LeweeLewee/Decca/mechanical/Drawings/Decca_IEC_C14_Mounting_Plate_Work_Handover.md

# Work Handover — Decca IEC C14 Mounting Plate

> **SUPERSEDED 2026-09-06.** The Rev A build described by the original handover was completed but **failed physical review** because its rectangular C14 opening did not properly enclose the actual inlet profile. Do not repeat or release Rev A.
>
> The active design is **Rev B**, controlled by `mechanical/Drawings/Decca_IEC_C14_Mounting_Plate_Spec_revB.md` and documented in `mechanical/Drawings/Decca_IEC_C14_Mounting_Plate_revB_Build_Report.md`.
>
> Rev B uses all four supplied profile measurements: 27.14 mm overall/long flat, 19.50 mm overall height, 16.00 mm opposite short flat and 14.00 mm straight side. These derive each angled side as 5.57 mm run × 5.50 mm rise = 44.638°. Nominal corners are R2.00 at the two long-flat corners and R0.40 at the other four. The production opening applies 0.25 mm normal clearance and is rotated 90° in the plate.
>
> Rev B CAD and exported STEP/STL pass 15/15 checks. Status remains **CAD PASS / physical prototype fit pending**.

The original Rev A handover has been intentionally replaced by this supersession notice so an automated worker cannot accidentally execute the rejected rectangular-opening design. Historical Rev A geometry, rationale and failure evidence remain in `Decca_IEC_C14_Mounting_Plate_Spec_revA.md` and `Decca_IEC_C14_Mounting_Plate_revA_Build_Report.md`.
