LeweeLewee/Decca/mechanical/Drawings/Decca_OLED_Display_Mount_Topology_revP.md

# Decca OLED Display Mount — Rev P Topology Review (pre-CAD gate)

Stage 1 deliverable required by `Decca_OLED_Display_Mount_CAD_Review_revO.md` §11.
No Fusion geometry may be generated until this section is clean.

> **Rev P.2 — CORRECTED 2026-08-29 after a physical retention failure.**
> The printed Rev P.1 carrier failed its retention test: the OLED falls forward
> through the loose carrier. The failure is **architectural, not a tolerance
> adjustment**. §0 records it; §1–§10 are the corrected topology and supersede
> the Rev P.1 text entirely.
>
> **Rev P.2 then PASSED physically** for OLED retention and Perspex tolerance.
> §1–§10 therefore describe validated hardware and are carried forward
> unchanged.
>
> **Rev P.3 — BOUNDED AMENDMENT 2026-08-29.** Two integration failures against
> the radio, neither touching the validated OLED architecture:
>
> - **§11** the continuous end rail and its cable-tie projection collide with
>   the retained original Decca lighting unit and are deleted;
> - **§12** the original front bolts have a non-standard thread, so the whole M2
>   heat-set-insert architecture is deleted and the original bolts and their
>   matching nuts are reused with a captive hex pocket.
>
> **Rev P.4 — BOUNDED CORRECTION 2026-08-29.** Two corrections to Rev P.3,
> again leaving the validated OLED architecture alone:
>
> - **§11.5** the synthetic lighting-unit keepout component is **deleted**. Its
>   boundary was asserted from the carrier's own pedestals, so it could never
>   have caught a real collision, and shipping it in the browser, the assembly
>   STEP and the manufacturing pack misrepresented the assembly. The physical
>   rail cut it was invented to justify is kept exactly as printed;
> - **§13** the open rear window is **closed** by an integral opaque rear light
>   shield, part of the carrier, with a single local four-pin/header opening.
>   §6 is amended accordingly: release was never rearward, and still is not.
>
> **Rev P.5 — MANDATORY AMENDMENT 2026-08-29.** Brief §5.3 and §8.4 together.
> These interact, so they are applied as one controlled update:
>
> - **§14** both plain locating posts are **deleted** and replaced by sprung
>   locating-and-retaining posts. Every one of the four PCB mounting holes now
>   holds a split sprung post. No plain-post parameter, body, branch, probe or
>   report entry survives;
> - **§15** the complete OLED reference is rotated **180° in plane**, so the
>   four-pin connector is at the **bottom**, and the visible active area is
>   dropped until its bottom edge meets the Perspex opening bottom edge. The
>   panel-fixed holes do **not** move;
> - **§16** the carrier drops to **6.00 mm** deep, the finished rear opening
>   grows 25% to **14.00 × 4.19 mm**, and two integral **light-block** baffles
>   are added beside it.
>
> **Nothing numeric is inherited.** The 2.00 mm depth reduction shortens every
> sprung cantilever, so both pairs are re-solved from the finished solid.
> §1–§10 remain the architecture; their *numbers* are superseded by §14–§16.

> **Rev P.5 MOUNTING-POINT CORRECTION, 2026-08-29.** Both carrier fixing
> centres move **7.00 mm toward the connector/open bottom** relative to the
> OLED-dependent group (`carrier_fix_y_from_previous = -7.00 mm`). The original
> Perspex holes do not move, so in the assembled frame the equivalent — and the
> only implementation that lands the carrier holes *on* the Perspex holes — is
> to raise the OLED bay and everything that depends on it by **+7.00 mm**.
>
> **This supersedes §15's active-area-bottom-to-opening-bottom rule**, and
> every PASS that depended on it. §17 records the correction and, plainly, what
> it does to the visible screen.

Baseline: `main` @ `d7ac584`, whose §5.3, §8.1, §8.2, §8.3, §8.4, §9, §10 and
§12 are authoritative over anything written on this branch before them.

---

## 0. The Rev P.1 retention failure — what actually went wrong

Rev P.1 inserted the OLED **from the rear**, moving forwards towards the
Perspex. Its four snap-finger shoulders sat at the **PCB rear plane** (z = −2.70)
and stopped motion in the **opposite** direction — rearward, back out of the
pocket. Once the board passed those shoulders there was **no positive feature of
any kind** preventing further forward travel.

The only thing holding the module in a loose carrier was four 0.10 mm edge-grip
tongues pressing on the PCB **edge**, relying on an assumed PETG friction
coefficient. The Rev P.1 gate checked:

- that the rear shoulders exist — **they do, and they restrain the wrong way**;
- that the tongues stop behind the PCB front plane — **they do, which is exactly
  why they cannot stop forward travel**;
- that computed friction (0.55 N) exceeds module weight (0.039 N) — **a
  calculation, not a geometric stop**.

Nowhere did it demonstrate a positive geometric stop against forward movement,
because there was not one to demonstrate. The physical print settled it: the
screen falls out forwards.

**Conclusion.** Friction between a printed tongue and a PCB edge is not
retention. The gate must require *geometry that physically blocks the motion*,
and the module must be inserted from the side it is restrained on.

The following are **not** acceptable fixes and are not attempted: increasing
`finger_grip`, revising the assumed friction coefficient, increasing spring
force, or adding another rear-loaded edge finger. All four leave the
architectural defect in place.

### What survives from Rev P.1

The structural half of Rev P.1 was sound and is retained unchanged: the M2 load
path in parallel with the module, the direct carrier-to-Perspex hard stop, the
0.30 mm optical chain, the ≤ 1.00 mm front-side protrusion budget, the open
rear, active-area centring, the single printed carrier plus the Rev N bezel, and
the invariant-based way of proving that nothing structural sits in front of the
PCB.

### What is deleted

The four PCB-edge friction fingers, their shoulders, their 0.10 mm tongues,
their four Ø2.20 mm radial prise holes, and the friction-versus-weight
acceptance gate. None of them appears anywhere in Rev P.2.

---

## 1. Side section — insertion direction, both axial stops, the load path

Section on the plane x = +15.00 (through a sprung locating post), looking
along −X. `+Z` is forward, out of the fascia. `z = 0` is the rear face of the
Perspex. **The module is inserted from the FRONT, moving rearward (−Z).**

```text
                        FRONT (viewer)  —  INSERTION SIDE
   ═══════════════════════════════════════════════════════════   z = +3.00
     ORIGINAL bolt head bears here          ORIGINAL PERSPEX 3.00 mm
   ═════════════╤═══════════════════════════════════════╤═════   z =  0.00  <- DATUM A
                |                                       |           carrier hard stop
                |         v  v  v  MODULE INSERTED      |           (seating plane)
                |         v  v  v  FROM THIS SIDE       |
                |                                       |
                |        <- optical gap 0.30 mm ->      |       z = −0.30  glass front
                |   ┌────────────────────────┐    /^\   |       z = −0.40  nose tip
   ┌────────────┤   |       OLED GLASS       |   /   \  |       (Ø2.60, 0.40 clear
   |            |   |   (0.80 proud of PCB)  |  | Ø3.2| |        of the Perspex)
   |  CARRIER   |   |                        |  ├─────┤ |       z = −0.75  land
   |    RIM     |   ├────────────────────────┤  ├█████┤ |       z = −1.00  <- SNAP HOOK
   |  (3.00)    |   |        OLED PCB        |  |     | |        retaining face, square,
   |            |   |        1.60 mm         |  |     | |        0.10 mm axial clearance
   |            |█  |                        |  |Ø2.80| |       z = −1.10  PCB front face
   |            |█  |                        |  |shaft| |       z = −1.20  fwd material
   |            |█  └────────────────────────┘  |     | |                  limit (rim)
   |            |█══════════════╤═══════════════╪═════╪═|       z = −2.70  <- DATUM B
   |            |█  ███████████ | FIXED DATUM   |     | |        PCB REAR FACE seats on
   |            |█  ██pedestal█ | PAD Ø6.0/Ø4.8 |     | |        FIXED, RIGID pads
   |            |█  ███████████ └───────────────┤     | |       z = −3.00  pedestal top
   |            |█  ██████████  Ø4.80 root  ████|     | |
   |            |█  ██████████     relief   ████|     | |        (the relief is now
   |  M2 boss   |█  ██████████  (3.20 deep) ████|  \_/| |         BEHIND the PCB — the
   |  + insert  |█  ████████████████████████████ \___/  |         glass cannot constrain
   |            |█  ██████████████ R0.80 fillet ────────┘         its depth any more)
   |            |█  ████████████████████████████████████  z = −5.90  post root
   |            |█  ████████████████████████████████████
   └────────────┴──█████████████████████████████████████         z = −8.00  carrier rear
                        REAR (cabinet)  —  OPEN                  z = −10.80 header extent

   █ = rigid carrier body (pocket wall / pedestal).
   The ONLY sprung element anywhere in the carrier is the split post nose.
```

### The two positive axial stops

| Direction | Stopped by | Nature |
|---|---|---|
| **Rearward** (−Z, the insertion direction) | four **fixed datum pads** at z = −2.70, rigid parts of the carrier body, concentric with the four PCB mounting holes | rigid solid-to-solid seat, no spring anywhere in the path |
| **Forward** (+Z, the direction Rev P.1 failed in) | two **sprung post hooks**, Ø3.20 barb over a Ø3.00 hole = **0.10 mm radial geometric overlap**, square retaining face at z = −1.00 | positive geometric interference — the retaining face is square and cannot cam, so an axial pull cannot release it |

Neither stop touches the glass:

- the rearward stop acts on the PCB **rear** face, 1.60 mm behind the glass;
- the forward stop acts on the PCB **front** face **inside the Ø3.00 mounting
  hole**, which is a keep-out on both faces of the board by definition;
- the glass front face is at z = −0.30 and nothing but air is in front of it.

**Neither stop is friction.** Friction plays no part in Rev P.2 retention and no
friction calculation appears in the acceptance gate.

### M2 load path — unchanged from Rev P.1

```text
ORIGINAL bolt head -> Perspex front face -> Perspex (3.00) -> Perspex rear
                   -> carrier seating rim + boss pad  (z = 0, DATUM A)
                   -> captive ORIGINAL nut -> original bolt thread

(Rev P.3: the M2 heat-set insert this line used to name is deleted - see 12)
```

The forward-most carrier material anywhere is z = 0. The forward-most module
material is the glass front face at z = −0.30. The carrier bottoms out on the
Perspex 0.30 mm before anything can reach the glass and 1.10 mm before anything
can reach the PCB. Carrier and module are in **parallel**, never in series, so
**M2 torque cannot reach the module** — it cannot alter OLED depth, preload the
glass or preload the PCB.

The snap hooks are not in the load path either: their tips stop at z = −0.40,
0.40 mm short of the Perspex, so tightening the screws never touches them.

---

## 2. Plan view — locating posts, datum pads, rear access

Rear view (looking forward, −Z). Dimensions in the aperture-centre frame.

```text
                    y = +30.60  ┌───────────────────────────────┐
                                |   cable-tie flange   ▭    ▭   |  tie slots x ±10.50
                    y = +24.60  ├───────┬───────────────┬───────┤
                                |       | wire notch    |       |  13.0 x 1.5 rear-open
                    y = +21.60  |   ┌───┴───────────────┴───┐   |  <- aperture edge
                    y = +21.00  |   |                       |   |  <- pocket wall
                    y = +20.75  |   ├───────────────────────┤   |  <- PCB top edge
                                |   |  ╭─╮   ┌───────┐  ╭─╮ |   |
                    y = +18.25  |   |  |S|   | header|  |S| |   |  <- SPRUNG POSTS
                                |   |  ╰─╯   └───────┘  ╰─╯ |   |     x ±15.00
                                |   |   ^ Ø8.6 pedestal ^   |   |
                                |   |                       |   |
   ●  M2 x = −24.50             |   |      OLED  PCB        |   |         M2 x = +24.50 ●
   y = 0 ──────────────────────-|   |     35.40 x 33.50     |   |-────────────────── y = 0
                                |   |   centre y = +4.00    |   |
                                |   |  ┌─────────────────┐  |   |
                                |   |  |  ACTIVE  AREA   |  |   |  29.42 x 14.70
                                |   |  |  centred (0,0)  |  |   |  <- OPTICAL DATUM
                                |   |  └─────────────────┘  |   |
                                |   |  ╭─╮           ╭─╮    |   |
                    y = −10.25  |   |  |P|           |P|    |   |  <- PLAIN POSTS
                                |   |  ╰─╯           ╰─╯    |   |     x ±15.00
                    y = −12.75  |   ├───────────────────────┤   |  <- PCB bottom edge
                    y = −13.00  |   |                       |   |
                    y = −13.60  |   └───────────────────────┘   |
                    y = −16.60  └───────────────────────────────┘
                                x = −21.55                x = +21.55
                                    (carrier rim, ±28.30 over the M2 ears)

   S = split SPRUNG locating post, Ø2.80 shaft / 0.70 slot / Ø3.20 barb
   P = PLAIN locating post, Ø2.70, top at z = −1.20 — never crosses the PCB
       front plane, so it is unconditionally clear of the glass
   Each post stands in a Ø4.80 root relief, on a Ø8.00 pedestal, ringed by a
   Ø6.00/Ø4.80 fixed datum pad at z = −2.70.
   Rev P.4: the rear of the bay is CLOSED by the 1.20 mm integral light shield
   (§13), with one local four-pin/header slot, x −5.60 … +5.60, y +17.15 upward.
   Header and cable exit through that slot; removal is forward, not rearward.
```

### Why the sprung pair is on the header side and the plain pair is not

The brief's default arrangement, and the reason for it, is this design's single
remaining risk:

| Hole pair | y | Modelled glass edge | Margin to a Ø3.20 nose | Post type |
|---|---:|---:|---:|---|
| Header side ("wide") | +18.25 | +13.95 | **+2.70 mm** | **sprung** |
| Display side ("narrow") | −10.25 | −9.05 | **−0.40 mm (fouls)** | **plain** |

On the modelled envelope the glass **overhangs the display-side mounting holes**.
That pair therefore gets **plain posts that stop at z = −1.20**, 0.10 mm behind
the PCB front plane. Nothing there ever crosses into glass territory, whatever
the real envelope turns out to be — the risk is removed by geometry, not by a
number.

Rev K put sprung pegs in the narrow pair on **0.20 mm of assumed glass
clearance** and called it validated. That unmeasured dependency is **not**
recreated here.

---

## 3. Locating and retaining posts — geometry and the Rev D/K inheritance

Starting values taken from the printed Rev D / Rev K post development, then
**recalculated from the finished Rev P.2 geometry** as the brief requires.

### 3.1 Sprung locating posts — x = ±15.00, y = +18.25

| z range | feature | Ø | note |
|---|---|---:|---|
| −5.90 … −5.10 | R0.80 root fillet | 2.80 → 4.40 | inside the Ø4.80 relief, top 2.40 mm behind DATUM B |
| −5.90 … −1.00 | split shaft | **2.80** | 0.10 mm radial clearance in the Ø3.00 hole |
| −1.10 … −1.00 | axial clearance zone | 2.80 | **0.10 mm** — the hook does not clamp the PCB |
| **z = −1.00** | **retaining face — square, rearward-facing** | 2.80 → **3.20** | **0.10 mm radial overlap = the forward stop** |
| −1.00 … −0.75 | full-diameter land | 3.20 | 0.25 mm, thicker than a print layer |
| −0.75 … −0.40 | insertion lead-in cone | 3.20 → 2.60 | 40.6° from the axis |
| slot | full height, 0.70 mm wide, normal to Y | | halves deflect **inward**, never outward |

### 3.2 Plain locating posts — x = ±15.00, y = −10.25

| z range | feature | Ø |
|---|---|---:|
| −3.70 … −2.90 | R0.80 root fillet | 2.70 → 4.30 |
| −3.70 … −1.65 | shaft | **2.70** (0.15 mm radial clearance) |
| −1.65 … −1.35 | entry chamfer | 2.70 → 2.10 |

Top face at z = −1.35 — **0.25 mm behind the PCB front plane**, so the plain
posts satisfy the original prohibition without needing the controlled exception
at all. 0.10 mm (the generic `forward_setback`) is too thin to trust on an FDM
post top when the modelled glass overhangs these holes; 0.25 mm costs nothing
and still engages 1.35 mm of the 1.60 mm board.

### 3.3 Reused, changed, and why

| Rev D / Rev K value | Rev P.2 | Change and reason |
|---|---|---|
| sprung shaft Ø2.80 | **Ø2.80** | reused unchanged — printed and fit-tested at Rev D |
| split slot 0.70 | **0.70** | reused unchanged |
| barb Ø3.20, 0.10 mm radial hook | **Ø3.20, 0.10 mm** | reused unchanged — the brief's starting value |
| R0.80 root fillet | **R0.80** | reused unchanged |
| plain post Ø2.70 | **Ø2.70** | reused unchanged |
| root relief ≈ 1.00 mm | **3.20 mm (sprung) / 1.00 mm (plain)** | **changed.** In Rev D/K the relief sat *in front of* the PCB, so its depth was capped by the glass — that is exactly what forced Rev K's narrow pair down to a 0.40 mm relief on 0.20 mm of assumed clearance. In Rev P.2 the relief is **behind** the PCB, where the glass cannot constrain it at all, so its depth is set by strain instead. |
| hook land (Rev D: under one print layer) | **0.25 mm** | **changed.** A retaining face thinner than a layer is not a retaining face. |
| Rev D peak strain 1.64 % (a = 3.10) | **0.83 %** (a = 4.35) | consequence of the deeper relief |
| Rev K narrow pair on 0.20 mm assumed glass clearance | **deleted** | replaced by plain posts — the dependency is removed, not re-estimated |

### 3.4 Recalculated mechanics

Cantilever half-post, fixed at the top of the root fillet (z = −5.10), loaded at
the full-diameter land (z = −0.75): free length **a = 4.35 mm**, half-section
thickness t = (2.80 − 0.70)/2 = **1.05 mm**, PETG E = 2000 MPa.

| Quantity | Value |
|---|---:|
| Deflection to pass the barb, per half | 0.10 mm |
| **Peak strain, hole centred** | **0.83 %** |
| Deflection worst case, board hard to one side | 0.20 mm on one half |
| **Peak strain, worst case** | **1.66 %** |
| Strain limit | 3.00 % |
| Radial spring force per post at 0.10 mm | ≈ 3.9 N |
| Insertion force (40.6° cam, µ 0.30) | ≈ 6.1 N per post → **≈ 12.3 N total** |
| Seated deflection | **0.00 mm — the barb clears the PCB entirely** |
| Seated radial preload on the PCB | **zero** (0.10 mm shaft clearance in the hole) |
| Seated axial preload on the PCB | **zero** (0.10 mm clearance under the hook) |
| PCB bending from retention | **none** |
| Forward retention mechanism | **positive geometric overlap**, square face, cannot cam |
| Bearing area of the two hooks | ≈ 3 mm² → far beyond a 0.039 N module |

The seated state is the important line. Once the board is home, **every spring
in the carrier is fully relaxed**. The hooks stand clear of the PCB by 0.10 mm
and the shafts clear the holes by 0.10 mm radially, so the module is held by
four rigid pads at its rear and blocked by two relaxed hooks at its front, with
nothing squeezing, bending or preloading it.

---

## 4. Fixed rear datum pads

Four annular pads, **rigid parts of the carrier body**, top face at z = −2.70:

| | |
|---|---:|
| Position | concentric with the four Ø3.00 PCB mounting holes, x ±15.00, y +18.25 / −10.25 |
| Outer Ø / inner Ø | 6.00 / 4.80 |
| Nominal annulus area | 10.18 mm² each |
| Area actually on the PCB (clipped by the 35.40 x 33.50 outline) | ≈ 8.6 mm² each, **≈ 34 mm² total** |
| Supported by | Ø8.00 pedestals, z −8.00 … −3.00, merged into the pocket walls |
| Spring content | **none** — solid carrier body throughout |

Why these four locations and no others: they sit **inside the PCB's own
mounting-hole keep-outs**, which are component-free on both faces by
construction. Every earlier revision took its PCB datum from the board edge
band, which is an assumption about where components are not. This one is not an
assumption.

They span a 30.00 x 28.50 rectangle — the widest stable four-point pattern the
board offers — so the seated board cannot rock. Loading is the ≈ 12 N insertion
push only; nothing pushes the module rearward in service. 34 mm² at 12 N is
0.35 MPa.

---

## 5. Invariant P1′ — the controlled exception, stated as geometry

Rev P.1's invariant P1 said the aperture prism is empty forward of the PCB face.
Rev P.2 needs positive forward retention, so the invariant is **tightened to name
its own exception** rather than relaxed:

> **Invariant P1′.** Let `A` be the module-aperture prism
> `{ |x| ≤ 18.55, −13.60 ≤ y ≤ +21.60 }` and let `N` be the two nose envelopes
> `{ (x ∓ 15.00)² + (y − 18.25)² ≤ 1.60², −1.20 < z ≤ −0.40 }`. Then
>
> `Carrier ∩ A ∩ { z > −1.20 }  ⊆  N`
>
> and `N` lies strictly inside the two Ø3.00 PCB mounting-hole corridors.

Everything else satisfies the original prohibition unchanged:

| Carrier feature | z extent | satisfies P1′ because |
|---|---|---|
| Seating rim / frame | 0 … −8.00 | outside `A` |
| M2 bosses + ears | 0 … −8.00 | \|x\| ≥ 20.50, outside `A` |
| Cable-tie flange | 0 … −8.00 | y ≥ +24.60, outside `A` |
| PCB pocket walls | −1.20 … −8.00 | z ≤ −1.20 |
| Post pedestals, datum pads, root reliefs | −2.70 … −8.00 | z ≤ −1.20 |
| Plain post shafts and chamfers | −1.20 … −3.70 | z ≤ −1.20 |
| Sprung post shafts | −1.00 … −5.70 | cross z = −1.20 only inside `N` |
| **Sprung post noses** | **−1.20 … −0.40** | **the declared exception `N`** |

There is still **no carrier plate, seating land, structural shoulder or other
load-bearing feature** between the PCB front face and the Perspex. `N` carries no
load, sets no datum, and touches the PCB only when the module is being pulled
forwards out of the carrier.

### What `N` must be proven clear of

| `N` vs | Result | Basis |
|---|---|---|
| the Perspex | **0.40 mm clear** — nose tip z = −0.40, Perspex z ≥ 0 | modelled from the measured 3.00 mm panel |
| the Rev N bezel | **clear** — the bezel lip lies inside \|x\| ≤ 17.45, \|y\| ≤ 7.50; `N` is at y ≈ +18.25 | Rev N geometry, unchanged |
| the active display area | **9.30 mm clear** in Y | active area 29.42 x 14.70 on (0,0) |
| solder joints / tips | **8.49 mm clear** in X | tips at x −3.91 … +4.91 |
| the insertion and removal corridor | **clear** — the corridor is a pure ±Z translation and `N` sits inside the hole corridor it is meant to occupy | §6 |
| **the OLED glass** | **NOT DEMONSTRATED — see §7** | the glass X/Y envelope has never been measured |

---

## 6. Insertion and removal

Pure ±Z translation. No tilt, no rotation, no lateral shift — the only motion
whose swept envelope is exactly the module cross-section extruded along Z.

**Insertion** (carrier off the panel, **seating face towards you**):

1. Offer the module to the **front** of the carrier, glass towards the carrier,
   header at the top. The glass enters the open module aperture, which is
   0.85 mm larger than the PCB all round.
2. The two sprung barb tips (Ø2.60 at z = −0.40) enter the two header-side
   mounting holes first and align the board.
3. The PCB rear face enters the pocket at z = −1.20 (0.25 mm clearance).
4. The barbs cam inward 0.10 mm per half against the hole walls; the plain posts
   enter the display-side holes.
5. The PCB rear face lands on the **four fixed datum pads at z = −2.70**. Motion
   stops there — on rigid carrier body, not on a spring.
6. As the PCB front face passes z = −1.00 the two barbs snap fully clear and
   relax to zero deflection, standing 0.10 mm ahead of the PCB front face.
   Their tips reach z = −0.40, so 0.70 mm of nose stands proud of the board.

Only the two intended sprung noses deflect at any point in that sequence.
Everything else the module touches is rigid.

**Removal** (identified tool path):

1. Remove the two original bolts and lift the carrier off the Perspex.
2. From the front, squeeze each barb inward with fine-nose tweezers or snipe
   pliers — 0.10 mm per half. The barbs stand 0.70 mm proud of the PCB front
   face and are completely exposed, because nothing at all sits in front of the
   PCB.
3. With a barb pinched, lift that corner clear. The module aperture is 0.85 mm
   larger than the PCB on every side, so a spudger reaches the board edge at
   z = −1.20 all round and levers it forward.
4. If more purchase is wanted, the board's top edge (y = +20.75) overhangs the
   carrier's own termination (y = +20.50) by 0.25 mm and is reachable from the
   **open lighting-unit side**, which §11 deletes the rail from and §13 does not
   close. Push forward there.
5. The plain posts then slide straight out.

No prise holes, no special tool, and no rigid feature anywhere in the corridor.

**Rev P.4: the rear wall does not trap the module.** §13 closes the rear of the
bay, so the Rev P.3 rear push-out is gone. Nothing else changes, because the
release was never rearward:

| Requirement | How it is met with the rear wall present |
|---|---|
| the sprung posts are deliberately released | pinch both barbs 0.12 mm per half with fine-nose tweezers; 0.70 mm of each nose stands proud of the PCB front face |
| release is performed from the front or accessible sides | from the front through the module aperture, assisted if wanted from the open lighting-unit side |
| the OLED withdraws through the front/Perspex side | removal travel is **+Z**, the same straight line as insertion, reversed |
| neither PCB nor bonded glass contacts the rear wall | the wall's front face is at z = −6.80 and the PCB rear face never leaves z ≥ −2.70: **4.10 mm** of clearance, at every point of the sweep |

**Swept corridor expectations** (verified numerically in Stage 2):

| Swept body, ±Z | vs carrier | why |
|---|---|---|
| OLED glass | must be **CLEAR** | the aperture is empty forward of z = −1.20 except `N`; `N` is at y +18.25 |
| Solder tips @ 1.00 mm | must be **CLEAR** | tips at x −3.91 … +4.91, `N` at x ±13.40 … ±16.60 |
| Header body | must be **CLEAR** | pedestals at \|x\| 11.00 … 19.00; header at x ±5.00 |
| OLED PCB | **HIT expected**, at the two barbs only | the designed 0.10 mm snap deflection and nothing else |
| Four mounting-hole corridors | **HIT expected**, posts only | the posts are meant to be there |

---

## 7. The one blocking measurement — reported, not assumed

The brief is explicit: *if the real glass envelope cannot be demonstrated clear,
stop and report the missing measurement rather than assuming it.*

**It cannot be demonstrated. It is reported here, and it is not assumed away.**

| | |
|---|---|
| Missing dimension | the OLED glass X/Y envelope relative to the two **header-side** Ø3.00 mounting holes at (±15.00, +18.25) |
| Status in this repository | **never measured.** `oled_glass_w`, `oled_glass_h` and `oled_glass_off_y` are flagged NOT MEASURED in every revision since Rev B. The only measured glass dimension is `oled_glass_proud` = 0.80 mm. |
| Modelled value | glass top edge at y = +13.95 → **2.70 mm clear** of a Ø3.20 nose |
| Acceptance criterion | **the glass must not extend above y = +16.15** — it must stay clear of Ø4.20 circles centred on the two header-side mounting holes (nose Ø3.20 + 0.50 mm margin all round) |
| How to measure | with the module in hand, digital calipers: distance from each header-side mounting-hole centre to the nearest bonded-glass edge. One number, both ends. It must be **≥ 2.10 mm**. |
| Consequence if it fails | the sprung noses foul the glass. The design does **not** proceed to a print on an assumption. |

Evidence that is *suggestive* but is deliberately **not** treated as proof: the
front-face solder pads sit at y ≈ +17.95 … +19.15, and bonded glass cannot cover
solder pads, which bounds a rectangular glass panel below y ≈ +17.95. That bound
is 1.80 mm short of what the nose needs, and it rests on the pad position rather
than on the glass itself. It is not sufficient.

Note also what the modelled envelope implies: it puts the glass **0.40 mm over
the display-side mounting holes**, which would make the module unmountable with
any screw. The modelled numbers are therefore known to be untrustworthy in
exactly this region — a further reason not to lean on them.

**Gate: no corrected Rev P print until this single number is taken.** Everything
else in Rev P.2 is complete and validated; this is the one item standing between
the CAD and the printer.

Contingency if the measurement fails: move the sprung pair outboard along X
within the keep-out, or fall back to a non-hole forward stop bearing on the PCB
**corners** outside the glass footprint. Both are small changes to the generator;
neither is designed until the number exists.

### The other unmeasured inputs, unchanged in status

| # | Item | Blocks CAD? | Blocks print? |
|---|---|---|---|
| 1 | `oled_glass_proud` = 0.80, single measured sample | no | no |
| 2 | **Glass envelope vs the header-side holes** | **no** | **YES — §7** |
| 3 | `oled_pcb_off_y` = 4.00 assumed — affects centring only | no | no |
| 4 | Front-side protrusion ≤ 1.00 mm | no | no — assembly preparation |
| 5 | Anything on the PCB front face other than glass and tips | no | flag at the fit test |

---

## 8. Resulting nominal Z-chain

| z (mm) | Feature |
|---:|---|
| +3.000 | Perspex front face — M2 heads bear here |
| **0.000** | Perspex rear face = **carrier structural hard stop (DATUM A)** |
| −0.300 | OLED glass front face — `oled_perspex_gap` |
| −0.400 | sprung post nose tip — 0.400 mm clear of the Perspex |
| −0.750 | barb full-diameter land begins |
| **−1.000** | **snap-hook retaining face — the forward stop** |
| −1.100 | OLED PCB front face — `+ oled_glass_proud 0.80`; **0.100 mm under the hook** |
| −1.200 | forward limit of all carrier material inside the aperture, `N` excepted |
| −1.350 | plain post tops |
| **−2.700** | OLED PCB rear face = **fixed datum pads (DATUM B)** — `+ oled_pcb_t 1.60` |
| −2.900 | plain-post root fillet top |
| −3.000 | post pedestal top |
| −3.700 | plain-post root relief floor |
| −5.100 | sprung-post root fillet top |
| −5.900 | sprung-post root relief floor |
| −8.000 | carrier rear face |
| −10.800 | header rear extent — clear of the carrier |

```text
oled_perspex_gap 0.30  +  oled_glass_proud 0.80  +  oled_pcb_t 1.60  =  2.70
```

Carrier: **56.60 W x 47.20 H x 8.00 deep**. The 9.60 mm depth of Rev P.1 existed
only to give its 8.40 mm cantilever fingers room; with the fingers deleted the
depth falls out of the M2 insert stack and the post reliefs instead.

Optical: active area 29.42 x 14.70 centred on (0, 0); aperture margin x 2.89,
y 0.30 — firmware must still mask 2 pixel rows top and bottom, unchanged since
Rev C.

---

## 9. Print orientation

**Carrier rear face flat on the bed, building forward (+Z). No supports.**

| Feature | In this orientation |
|---|---|
| Post pedestals | grow from the bed, fully supported columns |
| Root reliefs | upward-opening blind pockets — need nothing |
| Post roots | start on the solid relief floor, supported |
| Datum pads at z = −2.70 | upward-facing faces on a layer boundary — layer-count accurate |
| Aperture step at z = −1.20 | upward-facing ledge |
| Barb retaining face at z = −1.00 | a **0.20 mm** downward-facing annular ledge, the step from the Ø2.80 shaft to the Ø3.20 barb (the retention overlap against the Ø3.00 hole is a different 0.10 mm) — the Rev D / Rev K hook class, both of which printed |
| Barb lead-in cone | 40.6° from the axis, 49° from horizontal — self-supporting |
| Seating face at z = 0 | becomes a top surface — use 4+ top layers or ironing, as Rev P.1 |

No unsupported critical barb: the only overhang in the retention system is the
0.20 mm hook ledge, and it is short, small in area, and printed on top of a
solidly rooted column.

DATUM A (z = 0) and DATUM B (z = −2.70) lie in the same Z stack, so the 2.70 mm
between them is layer-count accurate.

---

## 10. Pre-CAD gate — self-review verdict

The brief forbids building CAD until this section demonstrates four things.

| Required demonstration | Shown | Where |
|---|---|---|
| **Rearward motion stops on fixed datum pads** | four rigid annular pads at z = −2.70 on Ø8.00 pedestals; no spring in the path | §1, §4 |
| **Forward motion stops on positive snap-hook overlap** | 0.10 mm radial barb-over-hole interference, square retaining face that cannot cam; no friction term anywhere | §1, §3 |
| **Neither stop loads the glass** | the rear stop acts on the PCB rear face 1.60 mm behind the glass; the forward stop acts inside a mounting-hole keep-out; both are relaxed when seated, zero preload | §1, §3.4 |
| **M2 torque cannot reach the module** | the carrier bottoms on the Perspex at z = 0, the module is forward-most at z = −0.30; parallel, not series | §1 |

| Other gate | Result |
|---|---|
| Insertion from the flush/Perspex side by a straight controlled motion | PASS — pure −Z, §6 |
| Only intended sprung noses deflect during insertion | PASS — two split posts; everything else rigid, §6 |
| Retention by positive geometry, not friction | PASS — no friction term in the design or the gate, §3.4 |
| Hooks retain without clamping or bending the PCB | PASS — 0.10 mm axial clearance, 0.10 mm radial clearance, zero seated preload |
| Plain and sprung posts locate X/Y | PASS — four posts in four holes, §2 |
| No carrier plate / land / structural shoulder ahead of the PCB face | PASS — invariant P1′ with a single declared, bounded exception, §5 |
| Carrier-to-Perspex hard stop carries all M2 preload | PASS — DATUM A, §1 |
| No separate retainer bar | PASS — two printed parts, carrier + unchanged Rev N bezel |
| Removal possible with an identified tool path | PASS — §6 |
| Print orientation supports the roots, no unsupported critical barb | PASS — §9 |
| **Glass clearance for the two snap noses** | **NOT DEMONSTRATED — blocks the print, not the CAD, §7** |

> **Historical — this is the Rev P.2 pre-CAD gate.** Both items it left open
> are now closed: the Rev P.2 prototype passed its retention test, and the
> Rev P.5 prototype passed the full physical test set including glass
> clearance. See the build review §29.

**Topology approved for CAD**, with §7 recorded as the one blocking item that
must be measured before a corrected carrier is printed. The physical retention
finding from Rev P.1 remains **OPEN** and can only be closed by a real inversion
and gentle-shake handling test on a printed part.

---

# Rev P.3 amendment — the radio-side interface

Everything above is validated hardware and is unchanged. The two sections below
are the only design changes.

---

## 11. Original Decca lighting-unit side (brief §8.1)

### 11.1 What collided

The lighting unit is original, retained and cannot be removed. The Rev P.2
carrier put a **continuous transverse rail** across the two side uprights on
that side (y +21.60 … +24.60, full 43.10 mm width) and stood a **cable-tie
flange** on top of it reaching y +30.60, with a rear relief and two tie slots.
The rail and that projection foul the lighting unit.

### 11.2 What is deleted

- the complete continuous end rail on the lighting-unit side;
- its central integral cable-tie / strain-relief projection;
- both tie slots and the flange rear relief;
- the rear-open wire notch that passed through the flange root.

Nothing is put back inside the keep-out. Parameters `top_flange`, `flange_w`,
`wire_notch_w`, `wire_notch_depth`, `tie_relief_w`, `tie_relief_h`,
`tie_relief_depth`, `tie_slot_x`, `tie_slot_w`, `tie_slot_h` and `tie_slot_z`
are gone from the generator, and the cable-tie path check is gone from the
validation gate.

### 11.3 What is retained

| Retained | Evidence |
|---|---|
| both sprung posts, full Ø8.60 pedestals, Ø6.00 datum pads, Ø4.80 reliefs, R0.80 root fillets | probed intact at both posts, in both tools |
| the local pedestal-to-side-upright connections | solid at the upright inner face on both sides |
| both vertical side uprights | terminated and capped, §11.4 |
| both 49.00 mm fixing-boss load paths | pitch measured 49.00000 mm exactly |
| the opposite transverse rail | untouched, y −16.60 … −13.60 |
| the OLED insertion, removal and wiring corridors | all corridors re-run CLEAR |

### 11.4 Where the carrier now ends, and how

```text
                    y = +22.55  ╭───╮           ╭───╮      <- pedestal tangent
                                │ S │           │ S │         = ASSERTED keep-out
                    y = +20.50  ├───┤           ├───┤      <- upright cap, R1.80
                                │   │  N O T H I N G  │
   ●  fixing        ┌───────────┘   │   B E T W E E N │
      x = −24.50    │  upright      │    T H E M      │
   ────────────────-┤               │                 ├──  ● fixing x = +24.50
                    │      OLED pocket, open at this end   │
                    │   ╭───╮                   ╭───╮      │
        y = −10.25  │   │ P │                   │ P │      │
                    │   ╰───╯                   ╰───╯      │
        y = −13.60  ├───────────────────────────────────────┤
        y = −16.60  └────────── bottom transverse rail ─────┘
```

The two side uprights stop at **y = +20.50**, half a millimetre short of the PCB
pocket wall line, and each is capped with a **half-round of its own 3.60 mm
width (R1.80)**. That radius lands directly alongside the retained sprung-post
pedestal root, which the pedestal ties into over a 6.26 mm long lens up to
1.35 mm deep — a real overlap, not a tangent touch.

Above y = +20.50 the only carrier material anywhere is the two Ø8.60 pedestal
towers. Between them, over x −10.70 … +10.70, there is nothing at all.

| | Rev P.2 | **Rev P.3** |
|---|---:|---:|
| Carrier extent on the lighting-unit side | y +30.60 | **y +22.55** |
| Projection returned | — | **8.05 mm** |
| Continuous bridge across the uprights | full width | **none** |
| Carrier height | 47.20 mm | **39.15 mm** |
| Carrier volume | 6.928 cm³ | **4.472 cm³** |
| Connected solids | 1 | **1** |

### 11.5 There is no keepout component — Rev P.4 correction

**Rev P.3 was wrong here and the error is corrected, not softened.**

Rev P.3 created a reference solid — `build_light_keepout()` /
`REF_Lighting_Keepout` / `LIGHTING_UNIT_KEEPOUT` — and checked the carrier
against it. Its boundary was placed at the **carrier's own sprung-pedestal
tangent**, y = +22.55, because the brief mandates retaining the full pedestals.

That is circular. A keep-out derived from the part it is meant to check can
never be violated by that part, so the check could not fail and proved nothing.
Worse, the body appeared in the Fusion browser, in the assembly STEP and in the
manufacturing pack, where a reader would reasonably take it for measured
lighting-unit geometry. **It was never measured. The lighting unit has never
been measured.**

Rev P.4 deletes all of it:

| Deleted | Where it was |
|---|---|
| `build_light_keepout()` | generator |
| component `REF_Lighting_Keepout` | Fusion browser, assembly STEP |
| body `LIGHTING_UNIT_KEEPOUT` | that component |
| derived `light_keepout_y` used only to place it | `derive()` |
| `carrier × lighting-unit keep-out solid` intersection gate | `validate()` §14 |
| `ORIGINAL_Nuts / ORIGINAL_Bolt_Envelope × lighting keep-out` gates | `validate()` §15 |
| `zero carrier material inside the keep-out solid` | independent verifier §M |
| its rows in the topology, build review, READMEs and exports | documentation |

Nothing replaces it. No proxy, no substitute body, no "conservative envelope".

**What is kept is the physical cut**, exactly as printed and offered up: the end
rail and cable-tie projection stay deleted, the uprights still terminate at
`light_cut_y` = +20.50 with their R1.80 caps, and the lighting-unit side stays
open. Only the *name* of the reported boundary changes: `light_keepout_y`
becomes **`carrier_max_y`**, and it now means what it always physically was —
*how far the carrier itself reaches on that side*, +22.55, down from +30.60.

Both tools now say so explicitly:

> CAD cannot and does not prove lighting-unit clearance. Brief §12.14, the
> installed physical test with the lighting unit left in place, is the sole
> authority for that interface, and it remains **open and mandatory**.

### 11.6 Strain relief

The integral cable tie is gone and is **not replaced**. The brief permits a
replacement only outside the keep-out and only with separately demonstrated
radio-side clearance, which does not exist. With the rail deleted the header and
loom now leave through a fully open end rather than a notch. Strain relief is an
open item.

### 11.7 Rack and twist

A closed frame has become an open one, so this is a real question. What carries
it: a 3.00 × 8.00 mm bottom transverse rail across the full width, two 3.00 ×
8.00 mm side uprights 37.10 mm long, both fixing arms and bosses, a 637.7 mm²
rear face, and the two pedestals tying the uprights into the module pocket. The
seated OLED itself also spans between the uprights. CAD can only report the
sections — **brief §12.15 is the actual test**.

---

## 12. Original Decca bolt and captive-nut interface (brief §8.2)

### 12.1 What is deleted

The original front bolts have a **non-standard thread**. The entire M2 heat-set
insert architecture is removed from the generator, the geometry and the
manufacturing pack:

| Deleted | Was |
|---|---|
| `m2_insert_d` | 3.20 |
| `m2_insert_depth` | 4.00 |
| `m2_insert_recess` | 0.50 |
| `m2_bore_chamfer` | 0.40 |
| cylindrical heat-set insert bores | 2 blind bores |
| insert backing calculation | `carrier_depth + z_insert_bore` |
| M2 heat-set insert BOM entry | 2 × Ø3.2 × 4.0 |
| replacement M2 screw BOM entry | 2 × M2×6 |

`m2_boss_d` and `m2_arm_h` are renamed `fix_boss_d` and `fix_arm_h`: they are
now structural boss and arm dimensions with no thread implication.

### 12.2 The measured nut — the across-flats reading, now confirmed

> **CONFIRMED 2026-08-30.** The 3.80 mm **is** across opposite flat faces. It
> was carried as an interpretation through Rev P.3–P.5 and flagged for checking;
> the check is done and the reading is correct. No number changes.

| Named parameter | Value | Status |
|---|---:|---|
| `original_nut_hex_width` | **3.80 mm** | **ACROSS FLATS — CONFIRMED 2026-08-30** — see §12.6 |
| `original_nut_head_seat_depth` | 1.40 mm | measured axial head seat |
| `original_nut_total_length` | 10.00 mm | measured, must be cleared in full |
| `nut_pocket_fit_allowance` | 0.20 mm | **printer/material fit**, coupon-validated |
| `nut_body_allowance` | 0.20 mm | clearance bore beyond the head across-corners |
| `nut_seat_depth` | 2.00 mm | solid carrier ahead of the seating shoulder |
| `nut_retain_lip` | 0.25 mm | captive retaining ridge |
| `bolt_clear_d` | 2.60 mm | original bolt shank clearance (panel hole 2.40) |

**Nothing here is derived from an M2, BA, UNC, metric or other catalogue nut.**
The pocket fit allowance is a print-process fit; it is not permission to alter
the 3.80 mm physical measurement.

### 12.3 The pocket, front to rear

```text
   z =  0.00   carrier seating face on the Perspex          DATUM A
               ┌──────────────┐
               │  Ø2.60 bolt  │   solid carrier ring, 2.00 mm, carries the
               │  clearance   │   clamp load in pure compression
   z = -2.00   ├──┬────────┬──┤   ◄── SEATING SHOULDER, 8.55 mm² annulus
               │  │ 4.00af │  │   regular-hex HEAD SEAT, anti-rotation,
               │  │  hex   │  │   exactly the 1.40 mm measured head seat
   z = -3.40   │  ├─┬────┬─┤  │   ◄── step: this is what makes 1.40 positive
               │  │ │3.55│ │  │   RETAINING RIDGE, 0.125 mm per flat
   z = -3.70   │  ├─┴────┴─┤  │
               │  │ \    / │  │   self-supporting lead-in, aligns the hex
   z = -4.10   │  ├────────┤  │
               │  │ Ø4.82  │  │   clearance bore for the rest of the nut
               │  │  bore  │  │
   z = -8.00   └──┴────────┴──┘   carrier rear face — pocket opens here
                     │    │
                     │    │       the last 4.00 mm of the 10.00 mm nut sits
   z =-12.00         └────┘       behind the carrier in free air
```

Boss Ø7.60 around it, minimum continuous wall **1.391 mm** at the clearance-bore
diameter, measured 1.388 mm off the exported mesh.

### 12.4 What each requirement is met by

| Requirement | Met by | Evidence |
|---|---|---|
| rear-accessible regular-hex anti-rotation pocket | 4.00 mm across-flats hex, opening at the rear face | measured 4.000 af / 4.619 ac off the mesh at both centres; the same nut rotated 30° interferes by 1.02 mm³ |
| positive axial seating shoulder | annulus at z = −2.00 | 8.55 mm², backed by 2.00 mm of solid carrier |
| defined 1.40 mm head-seat depth | hex head seat ended by a step to the ridge | not dependent on the nut crushing into plastic |
| clearance for the full 10.00 mm nut and engaged bolt | hex + Ø4.82 bore through to the rear | nut and bolt envelopes CLEAR of glass, PCB, header and Perspex |
| sufficient continuous boss wall | Ø7.60 boss | **1.391 mm** minimum, continuous |
| serviceable captive retention | 0.25 mm retaining ridge, 0.125 mm per flat | pushed past on assembly; **no adhesive**; a 2.2 mm pin through the bolt bore pushes it back out |

The nut is modelled at its full 3.80 mm across flats over the whole 10.00 mm —
the most pessimistic reading — and the **only** carrier/nut interference
anywhere is the declared retaining ridge. That is the same discipline used for
the OLED snap noses: interference is permitted only where it is the point.

### 12.5 Load path

```text
original bolt head → Perspex → carrier seating face / hard stop
                   → captive original nut → original bolt thread
```

No part of it passes through the OLED glass or the PCB: the glass is 0.300 mm
behind the seating plane and the PCB 1.100 mm behind it, and the bolt envelope
is CLEAR of both. The bolt never touches the carrier — it only pulls the nut
onto the shoulder.

### 12.6 Measurements that gate the print

| # | Item | Why it matters |
|---|---|---|
| 1 | **nut across flats AND across corners** | 3.80 mm is modelled as across flats. If it is across corners, the true across-flats is 3.29 mm and this pocket is 0.51 mm oversize. Change the one parameter and regenerate. |
| 2 | **original bolt length under the head** | must exceed the 5.00 mm grip (Perspex 3.00 + carrier 2.00) to engage at all, and stay under 15.00 mm to remain inside the nut. Neither end is measured. |
| 3 | **hex-pocket fit coupon** | `nut_pocket_fit_allowance` 0.20 and `nut_retain_lip` 0.25 are not yet demonstrated on this printer/material. `Hex_Pocket_Fit_Coupon_revP.stl` carries the same pocket at 0.10/0.15/0.20/0.25/0.30, notch-numbered. Print it first. |

---

## 13. Integral rear light shield (brief §8.3) — Rev P.4

### 13.1 What was wrong

Rev P.3 left the OLED bay open right through to the rear face: the PCB pocket
was cut from z = −1.20 to beyond z = −8.00 over the full 35.90 × 34.00 mm
footprint. Installed, the retained Decca cabinet LEDs sit on the other side of
that opening. They can light the rear and the edges of the OLED directly, which
shows as a glow through the Perspex aperture and as washed-out contrast on the
display. Nothing in the carrier stopped it.

### 13.2 The wall

One continuous wall, **integral to `Rear_Display_Carrier`** — not a cover, not a
second component, not a separate printed part.

| Property | Value | Why |
|---|---|---|
| named parameter | `rear_light_shield_t` = **1.20 mm** | 3 × 0.40 mm nozzle extrusion width. On a different extrusion width, raise it to at least three *actual* widths and regenerate |
| Z extent | −8.00 → **−6.80** | grown **forward** from the existing rear plane, so the external envelope is unchanged at 56.60 × 39.15 × 8.00 mm |
| X extent | −17.95 … +17.95 | exactly the PCB-pocket footprint, so it lands on both pocket side walls and bridges the two uprights **across the OLED bay only** |
| Y extent | −13.00 … **+20.50** | bottom rail up to `light_cut_y`. It stops where the carrier stops |
| clearance to the PCB | **4.10 mm** behind DATUM B | never touches the board, never preloads it, is never an OLED Z datum |
| connectivity | one lump, 3442 welded vertices, 1 connected component | joined continuously to the frame |
| material | **opaque black**, printed fully solid | solid perimeters through the wall — never sparse infill, never a single translucent skin |

It does **not** extend into or recreate the deleted end-rail / cable-tie region.
That material began at the pocket line y = +21.00 and ran outboard to +30.60;
the wall stops 0.50 mm short of the pocket line and 10.10 mm short of where the
flange was.

### 13.3 The only penetration — the four-pin opening

```
                y = +20.50  ── wall's free top edge = the open §11 side ──
                  ┌───────────────┐
   solid wall     │  PIN SLOT     │      solid wall
   12.35 mm       │ 11.20 × 3.35  │      12.35 mm
                  └───────────────┘
                y = +17.15  ── slot floor, solid wall below ──
                     x −5.60 … +5.60
```

Sized from the existing header reference parameters plus two **separate, named**
clearances, so it can be adjusted without touching the general OLED opening:

| Input | Value |
|---|---|
| `oled_header_w` | 10.00 mm |
| `oled_header_h` | 3.00 mm |
| `oled_header_off_y` | +19.25 mm |
| `oled_header_depth` | 8.10 mm rearward of the PCB rear face → z = −10.80 |
| `pin_slot_clear_x` | **0.60 mm** per side — print allowance + conductor room |
| `pin_slot_clear_y` | **0.60 mm** — print allowance + the wire bend |

Result: **11.20 × 3.35 mm**, 37.52 mm² — **3.1 %** of the 1202.65 mm² wall. It
is aligned on the header centre, it passes completely through the wall, and the
full 8.10 mm header/wiring envelope crosses it with **zero** contact. The wire
bend immediately behind the header lies inside that same envelope, 2.80 mm past
the rear face, so it is covered by the same check.

There is no general rear window, no solder-access window and no rear release
opening. A swept membership test over the whole bay slab — 4757 points — finds
material everywhere except inside this slot.

### 13.4 Reported, not hidden: the slot's top boundary

The header row sits at `oled_header_off_y` = +19.25 and its envelope tops out at
**+20.75**. The carrier's own termination on that side is **+20.50**. The
connector is therefore at the *open* lighting-unit end of the board, 0.25 mm
proud of where the carrier is allowed to reach.

So the slot is bounded by wall on **both X sides** and **below**, and above by
the wall's free edge. That edge **is** the mandated open lighting-unit side of
§11 — it is not a second opening, and there is nothing above it to open.

Enclosing the slot would mean printing material back above y = +20.50, across
the two uprights, in exactly the band the physically-successful rail cut
emptied. That is not done. The alternative — dropping the wall below the header
so no slot is needed — would leave a 3.15 × 35.90 mm open band, i.e. a general
rear window under another name. Also not done.

If the powered test (§12.22) shows leakage **only** at this opening, the fix is
to tighten it locally or add a short integral hood — never to reopen the wall
and never to add another printed component.

### 13.5 What the wall does not change

| Preserved | Evidence |
|---|---|
| front/Perspex-side insertion | swept corridor CLEAR, unchanged |
| fixed rear PCB datum pads | 39.76 mm² still facing forward at z = −2.70 |
| plain and sprung locating posts | built before the wall; the wall cuts none of them |
| positive loose-carrier retention | 0.10 mm hook overlap, unchanged |
| deliberate OLED removal | §6, revised — still forward, never rearward |
| OLED Z position and 0.30 mm Perspex gap | optical chain untouched |
| active-area centring | untouched |
| 35.20 × 15.30 aperture, 49.00 mm pitch | untouched |
| captive-nut interface, hard-stop load path | pockets at x ±24.50, 6.55 mm outboard of the wall |
| the §11 rail cut | wall stops at +20.50; the old rail band stays empty |

### 13.6 Print orientation

Unchanged: **rear face on the bed, building +Z**. That makes the wall the
**first 6 layers**, laid flat on the bed over its full 35.90 × 33.50 mm area.
No bridging, no supports, and the four-pin slot is a through-slot in those same
layers. Its free top edge is a 1.80 mm strip beyond the upright cap line —
1.20 mm thick and 35.90 mm wide, a plate edge rather than a sliver or an
unsupported cantilever. The sliver check reports 0 faces < 0.02 mm² and 0 edges
< 0.05 mm.

---

## 14. Four sprung retaining posts (brief §5.3) — Rev P.5

### 14.1 What is deleted

| Deleted | Where it was |
|---|---|
| `plain_post_d`, `plain_relief_d`, `plain_relief_depth`, `plain_lead`, `plain_setback` | parameter table |
| `plain_post()` | generator |
| `d["plain"]` coordinate list, `z_plain_floor`, `z_plain_top`, `plain_clear` | `derive()` |
| the plain root-relief bore and the plain construction branch | `build_carrier()` |
| three plain-post point probes and the "plain posts stay behind the PCB front plane" gate | `validate()` |
| the plain-post shaft row, the plain-post P1′ box set and the "display-side pair is safe at any glass size" note | independent verifier |
| every plain-post line in the topology, build report and images | documentation |

Nothing is left that could quietly behave like a plain post: the verifier now
measures a **split slot** and a **retaining barb** at every one of the four
holes, and a plain post has neither.

### 14.2 The two pairs

Both pairs are split sprung locating-and-retaining posts. The converted pair
carries its own `sprung_far_*` names so it can be reduced once the bonded glass
is measured, **without disturbing geometry that has physical evidence behind
it**.

| | connector pair | converted far pair |
|---|---|---|
| position after the transform | x ±15.00, **y −18.55** | x ±15.00, **y +9.95** |
| shaft | 2.80 | `sprung_far_shaft_d` 2.80 |
| split slot | **1.20** | `sprung_far_slot_w` **1.20** |
| barb | 3.20 | `sprung_far_barb_d` 3.20 |
| nose tip | 2.60 | `sprung_far_tip_d` 2.60 |
| root relief | Ø4.80 × **2.00 deep** | `sprung_far_relief_d/depth` Ø4.80 × **2.00** |
| root fillet | R0.80 | `sprung_far_root_fillet_r` R0.80 |
| split rotation | 0° | `sprung_far_split_angle` **0°** |

`sprung_far_split_angle` is modelled and functional but set to 0°: rotating the
split does not change the barb's swept envelope, so it buys nothing against the
glass. It is there so the option survives the measurement.

### 14.3 Recalculated mechanics — nothing inherited

Both pairs come out identical, because both face the same 6.00 mm envelope.

| Quantity | connector | far | note |
|---|---:|---:|---|
| radial hook overlap | **0.100 mm** | **0.100 mm** | barb 3.20 in a Ø3.00 hole |
| insertion cam angle | 40.6° | 40.6° | 49.4° self-supporting cone |
| required deflection, per half | 0.100 mm | 0.100 mm | the overlap |
| nominal peak strain | **1.21 %** | **1.21 %** | limit 3.00 % |
| worst-case off-centre strain | **2.42 %** | **2.42 %** | 0.20 mm on one half; 19 % margin |
| insertion force per post | **7.1 N** | **7.1 N** | µ 0.30, estimate only |
| **combined four-post force** | **28.6 N** | **28.6 N** | total, all four; at the old 0.70 slot it would be 64.6 N |
| PCB bow, worst case | **0.057 mm** | **0.057 mm** | all 28.6 N at mid-span; under the 0.10 mm hook clearance |
| root section at the built-in point | 0.80 × 2.80 mm | same | exactly two 0.40 mm perimeters |
| material behind each relief | **1.30 mm** | **1.30 mm** | ≥ the 1.20 mm shield |
| clearance to the rear shield | **0.10 mm** | **0.10 mm** | relief floor to shield inner face |
| clearance to the light blocks | 2.50 mm+ | n/a | blocks stop at x ±11.94 |
| release deflection / travel | 0.100 / 0.70 mm | 0.100 / 0.70 mm | elastic, 1.45 % strain |

**Two proven values had to change, and both are consequences of §16's 6.00 mm
depth, not preferences.**

- **Split slot 0.70 → 1.20 mm.** The relief can no longer be 3.20 mm deep, so
  the cantilever falls from 4.35 to 3.15 mm. Strain goes as 1/a², so the proven
  0.70 slot would give **3.17 %** worst-case — over the limit — and 64.6 N of
  combined insertion force. Opening the slot thins each half from 1.05 to
  0.80 mm and brings those to 2.42 % and 28.6 N. 0.80 mm is exactly two 0.40 mm
  extrusion widths, where 1.05 mm was two perimeters plus a sliver.
- **Root relief 3.20 → 2.00 mm.** At 3.20 the bore would end 0.10 mm short of
  the rear face and cut clean through the 1.20 mm light shield. At 2.00 it
  leaves a **1.30 mm** solid floor — the shield thickness plus 0.10 mm — so the
  shield stays light-tight under every post.

Neither change weakens retention. Retention is the **square land** at
`z_hook_face` bearing on the PCB front face; a forward load on that land has no
inward component, so it cannot deflect a barb out of its hole at any stiffness.
Stiffness sets insertion and release effort only.

### 14.4 The bonded glass — this is the print gate

| hole pair | y | modelled glass edge | gap | keep-out needed | margin |
|---|---:|---:|---:|---:|---:|
| connector | −18.55 | −14.25 | 4.30 | 2.10 | **+2.20** |
| far | +9.95 | +8.75 | **1.20** | 2.10 | **−0.90** |

Against the bare Ø3.20 barb the far pair is **−0.40 mm**. That is the number the
brief quotes and it is reproduced unchanged rather than tuned away.

**The modelled envelope is not evidence.** `oled_glass_w`, `oled_glass_h` and
`oled_glass_off_y` have never been measured. As modelled the glass spans
x ±17.25 and y −14.25 … +8.75, which puts **both far mounting holes completely
underneath the bonded glass**. A board like that could not be screw-mounted at
all. The model is kept unedited because replacing a wrong number with a
convenient one would hide the measurement that is actually needed.

**The far nose is not simply made smaller.** The only lever on the keep-out
radius is the barb, and its floor is the Ø3.00 hole radius — below that there is
no overlap and no retention. The 0.10 mm overlap is the only overlap figure with
physical evidence behind it: it is what Rev P.2 actually retained with.
Shrinking the barb would trade proven retention for a keep-out reduction that
*still* would not clear the modelled glass.

Both tools therefore report the three glass checks as **BLOCKED**, not passed
and not failed — a check against a fictional envelope can be neither. Set
`oled_glass_measured` (generator) / `GLASS_MEASURED` (verifier) once the real
boundary is entered and they become ordinary hard gates with no other change.

**Before print release:** measure hole centre to nearest bonded-glass edge at
**all four** holes; model that measured boundary; demonstrate full swept
clearance for every shaft, split, lead-in and nose through insertion, seating,
retention, release and withdrawal; and keep every sprung feature inside its
verified hole/glass keep-out.

### 14.5 The four-post release sequence

Four sprung posts cannot all be pinched at once, and the brief does not require
it — only that the board never needs all four inaccessible at the same time. It
is released **a row at a time, about the other row**:

1. remove the two original bolts and lift the carrier off the Perspex — nothing
   after this needs the radio;
2. pinch **both connector-side barbs** (y −18.55) and lift that edge 0.70 mm.
   The board pivots on the far pair, which stays engaged and keeps control of
   it. The pivot is **1.41°**; the 0.10 mm radial clearance in a 1.60 mm board
   allows **7.13°** before a hole binds on a shaft;
3. pinch **both far barbs** (y +9.95) and withdraw the module straight forward,
   out through the Perspex side.

Steps 2 and 3 are the same operation on opposite rows, so the order reverses if
the far pair is easier to reach.

| Requirement | How it is met |
|---|---|
| no other rear-wall opening | removal travel is +Z; the wall is 2.10 mm behind the PCB rear face and never enters the path |
| the rear shield is not removed or damaged | it is never touched — nothing acts on it |
| nothing levers against the glass | every tool contact is a nose at z −0.40 or the PCB edge at z −1.20; the glass front face at z −0.30 is never a reaction surface |
| no post permanently deformed | 0.12 mm per half is **1.45 %** strain, the same as insertion, well under 3.00 % |
| not all four inaccessible at once | two rows, released independently |
| PCB mounting holes undamaged | the nose is squeezed clear **before** the board moves; the board is never dragged over an engaged barb |

---

## 15. The 180° module transform (brief §8.4) — Rev P.5

> **§15.2's vertical datum is SUPERSEDED by §17.** The 180° transform itself
> stands: the connector is at the bottom and the group is internally
> consistent. What changed is *where that group sits* — the fixing centres moved
> 7.00 mm toward the bottom, which raises the screen 7.00 mm in the assembled
> frame. The active-area figures below are the superseded baseline, kept only so
> the correction can be checked against a stated starting point.

The panel is the datum. The Perspex opening is centred on the origin, so its
bottom edge is at `−panel_open_h/2 = −7.65`. Aligning the visible active area's
bottom edge to it fixes the active centre at **y = −0.30**.

The transform is applied **once**, in `derive()`, to every module-local value —
PCB, glass, active area, all four mounting holes, header, solder tips, datum
pads, posts, pocket, rear-wall opening and light blocks. Nothing downstream
transforms anything again, so no feature can be moved twice or missed.

| Feature | module-local | after 180° + offset |
|---|---:|---:|
| active-area centre | 0.00 | **−0.30** |
| PCB centre | +4.00 | **−4.30** |
| glass centre | +2.45 | −2.75 |
| header centre | +19.25 | **−19.55** |
| connector-side holes | +18.25 | **−18.55** |
| far holes | −10.25 | **+9.95** |
| solder-tip rows | +18.55 / −10.55 | −18.85 / +10.25 |
| tip x offset | +0.50 | −0.50 |
| **fixing holes** | — | **y 0.00, pitch 49.00000 — NOT MOVED** |

Result at this stage: active area **horizontally centred**, connector at the
**bottom**, active centre at y −0.30. **That vertical position is superseded by
§17** — it survives here only as `oled_cy_prev`, the numerical baseline the
7.00 mm correction is measured from.

### 15.1 The open end travelled with the module — this matters

Brief §8.1 puts the open lighting-unit side *below/outboard of the connector-side
sprung pair*. That pair rotated from +Y to −Y, so **the cut travelled with it**:
the uprights now terminate at **y −20.80** instead of +20.50, and the solid
transverse rail is at +16.30.

> **The Rev P.3/P.4 installed fit does NOT carry over.** The carrier's open end
> is now on the opposite side of the panel-fixed bolts. Brief §12.14 is a
> **RE-TEST against the radio**, not a regression check. Both tools say so in
> their open items.

---

## 16. 6.00 mm depth, the enlarged opening and the light blocks (brief §8.4)

### 16.1 Depth

`carrier_depth` 8.00 → **6.00 mm**, measured Perspex seating plane to rear
plane. Everything recalculated from the finished 6.00 mm geometry:

| Clearance | Rev P.4 | **Rev P.5** | verdict |
|---|---:|---:|---|
| shield front face to DATUM B | 4.10 | **2.10 mm** | clear, no contact |
| relief floor thickness | 3.10 | **1.30 mm** | ≥ the 1.20 mm shield |
| relief floor to shield inner face | 1.90 | **0.10 mm** | no break-through, no membrane |
| R0.80 root fillet inside the relief | yes | **yes** | 2.00 mm relief, not truncated |
| nut clearance bore behind the lead-in | 3.90 | **1.90 mm** | ample |
| light-block front face to DATUM B | — | **0.50 mm** | behind the sweep |
| bolt grip | 5.00 | **5.00 mm** | unchanged |

Nothing was truncated to reach the depth. The cost is paid entirely in post
stiffness, and that is where §14.3 reports it.

### 16.2 The finished four-pin opening

Brief §8.4 fixes it at **14.00 × 4.19 mm** — 25 % up on the Rev P.4
11.20 × 3.35. Delivered by the two named clearances, symmetrically about the
transformed header envelope:

- width `= oled_header_w + 2 × pin_slot_clear_x = 10.00 + 2 × 2.00 =` **14.00**
- height `=` the header envelope grown by `pin_slot_clear_y = 1.44` each way,
  clipped below by the carrier's own termination `=` **4.19**

Measured off both the solid and the mesh. Still the **only** penetration: a
4757-point sweep of the bay finds material everywhere outside it.

### 16.3 The two internal light blocks

Two integral opaque baffles, one immediately outboard of each lateral edge of
the opening, growing **forward** off the shield's inner face to form a short
tunnel beside the pins.

| Property | Value |
|---|---|
| X | ±7.00 … **±11.94** — from the opening edge **out to the sprung pedestal, and 0.60 mm into it** |
| Y | −20.80 … −16.61, matching the opening |
| Z | −4.80 … **−3.20**, i.e. 1.60 mm forward off the shield |
| clearance to DATUM B | **0.50 mm** — behind the seated PCB, out of the sweep |
| clearance to the header | **2.00 mm** each side |
| thickness | 4.94 mm actual, against a 1.20 mm minimum (3 extrusion widths) |
| part of | `Rear_Display_Carrier` — one solid, not fins, not components |

**They run out to the pedestals deliberately.** Stopping at the nominal 1.20 mm
wall left a 2.50 mm open gap between each block and its tower — a straight
sideways path for light out of the pin opening into the bay, and visible in the
rendered part. The pedestal is a cylinder, so its inner edge retreats outboard
away from the post centre line; taking the tangent at the centre line would
leave a 0.04 mm slot at the block's far edge. The tie is therefore solved at the
**worst y the block reaches**, and both tools check the junction there.

They stay entirely **above** `light_cut_y`, inside the back-plate X/Y footprint
and inside the 6.00 mm Z envelope. The §8.1 rail cut is untouched.

### 16.4 One artefact removed while here

The rounded-rectangle corner radius is a cosmetic top-corner feature. Applied at
the cut end as well, it pulled the outer wall inward exactly where the R1.80
upright cap pushed it back out; the two crossed and left a visible **step in the
left and right outer walls**. The corner is now squared off over the cap band,
so each upright runs at constant width right down to its termination and the cap
lands tangent to it. The outer silhouette is a straight line from the transverse
rail to the cap. Nothing else moved, and the sliver check still reports 0 / 0.

---

## 17. Mounting-point correction — 7.00 mm (brief §8.4, amended)

### 17.1 The instruction, and the one place it is applied

**BOTTOM is −Y**: the open, cut-away side of the carrier that carries the
four-pin connector opening. Both carrier fixing centres move **7.00 mm toward
that bottom** relative to the complete OLED-dependent group:

```
carrier_fix_y_from_previous = -7.00 mm
```

The original Perspex and its holes are not moved, redrilled or redefined. So the
only implementation that puts the carrier holes **on** the Perspex holes rather
than 7.00 mm away from them is to hold `panel_fix_y` on the physical hole line
and **raise the OLED bay and everything that depends on it by +7.00 mm**.

`derive()` does exactly that, in one place: `oled_cy = oled_cy_prev + 7.00`.
Every OLED-dependent value is computed from `oled_cy`, so the whole group moves
together and cannot be half-moved:

| Moved with the OLED group | Not moved — panel-fixed |
|---|---|
| PCB reference, bonded glass, active area | both fixing bores |
| header / electrical connector, solder tips | both structural bosses |
| all four PCB holes and all four sprung posts | both captive-nut hex pockets |
| datum pads and pedestals | both nut-retention ridges |
| OLED pocket and the surrounding carrier frame | both fixing arms |
| rear light shield | the local hard-stop / load-path faces |
| the 14.00 × 4.19 mm connector opening | `panel_fix_y`, and the 49.00 mm pitch |
| both connector light-block walls | the Perspex patch and its opening |
| the open lower rail cut | |
| insertion and removal sweep geometry | |

### 17.2 The same move, stated in both frames

Both tools print both, and gate that they are one geometry:

| | before | after | change |
|---|---:|---:|---:|
| **carrier-local** — fixing centres relative to the OLED group | +0.30 | **−6.70** | **−7.00** |
| **assembled panel** — OLED group relative to the fixed Perspex holes | −0.30 | **+6.70** | **+7.00** |

Measured independently off the mesh: both bolt bores on one centreline at
y = 0.0000, Ø2.600, pitch **49.00000 mm**, symmetric about x = 0 — no X shift,
no skew. The fixings sit **15.847 mm** above the carrier's connector-side
extremity, against 22.85 mm before: **−7.00 mm**.

### 17.3 What it does to the visible screen — reported, not passed

The superseded rule is gone, and so is every PASS based on it. This is the
consequence, stated plainly:

| | y range | height |
|---|---|---:|
| active area | −0.65 … **+14.05** | 14.70 mm |
| Perspex opening | −7.65 … +7.65 | 15.30 mm |
| **visible overlap** | −0.65 … +7.65 | **8.30 mm** |

- **6.40 mm** of active area — about **44 %** — sits behind the fascia **above**
  the opening;
- **0.00 mm** sits below it;
- the lowest **7.00 mm** of the opening shows **unlit board**, not screen.

> **The active area is not fully visible and is not vertically centred.**
> Neither tool claims otherwise, and neither passes a check on it. Whether the
> intended screen information is still readable is a question only the powered
> fit test can answer — brief §12.8 / §12.26–27, photographed.

### 17.4 Structural re-check of the moved fixings

Sliding the fixings 7.00 mm relative to the OLED group lands them on a different
part of the side uprights, so the connection is **re-measured**, not assumed:

| Check | Result |
|---|---|
| both arms continuously joined to the uprights | solid across the full 7.50 mm arm height at the arm root (x ±19.55) and the upright outer face (x ±21.55) — a **2.00 mm** overlap, not a tangent |
| the arms land on full-width upright, clear of both corner radii | arm y −3.75 … +3.75; full-width upright y −9.00 … +20.30 — 5.25 mm below, 16.55 mm above |
| bosses clear the OLED bay | boss inner edge x ±20.70 against an aperture edge at ±18.55 — **2.15 mm** |
| nut pockets clear the rear shield and light blocks | nut bore inner edge x ±22.09 against a shield edge at ±17.95 |
| no thin neck, tangent-only join or sliver | **0 faces < 0.02 mm², 0 edges < 0.05 mm** |
| carrier-to-Perspex hard stops intact | **53.96 mm²** of the 406.4 mm² seating face is under the two arms; the bolt → Perspex → carrier seat → captive nut path is unbroken |
| nut-pocket boss wall | **1.391 mm**, unchanged — the pockets moved with their bosses |
| both bolts retain a valid clamp-load path | grip 5.00 mm, window 5.00–15.00 mm, unchanged |
| one connected solid | **1 lump**, 3446 welded vertices |
| carrier depth | exactly **6.00 mm** — the correction is in-plane only |
| all four sprung-post roots | unchanged: 1.30 mm floor, R0.80 fillet intact, 2.42 % worst strain |
| rear shield and light blocks relative to the OLED | unchanged — they moved with the group |
| connector opening | **14.00 × 4.19 mm**, unchanged |
| open connector side is still the bottom | rail cut at y −13.80, opening starts there, header entirely below the active centre |
| the deleted lighting-unit rail has not returned | nothing below y −13.80 but the two connector pedestal towers |

**One consequence to carry into the physical test.** The carrier now reaches
**y +23.30** above the bolt line, against +16.30 before, because the OLED bay
rose while the bolts stayed put. Nothing in CAD says whether that fits the
radio. Brief §12.14 covers it, and it is a physical test.

### 17.5 Assembly

The assembled Fusion model and the assembly STEP show the carrier fixing holes
**coincident** with the Perspex holes — never 7.00 mm apart. Re-checked after
the move: carrier × Perspex clear except the intended seating faces; bezel clear
of carrier, glass, PCB and tips; header and wiring corridors clear; the
OLED-to-Perspex gap still 0.300 mm; front insertion and the four-post release
sequence unchanged.

---

## 18. Rev P.5 pre-CAD gate — self-review verdict

> **CLOSED. The carrier was built, installed and tested, and every physical
> test passed.** The table below is the pre-CAD gate as it stood before the
> build. The rows marked BLOCKED or deferred to a physical test are now
> **closed by the prototype** — see the build review §29. Nothing in the table
> was changed to reach that state.

| Required demonstration | Result |
|---|---|
| Rev P.2 OLED architecture preserved unchanged | PASS — insertion, datum pads, posts, retention, release, Z position, gap, centring, aperture, pitch, hard stops and bezel all re-validated identical |
| Complete lighting-unit-side end rail deleted | PASS — nothing in its old y +21.60 … +24.60 band |
| Cable-tie projection and slots deleted | PASS — nothing in its old y +24.60 … +30.60 band |
| No bridge between the side uprights above the cut line | PASS — only the two pedestal towers, residual EMPTY |
| Nothing put back above the cut line | PASS — no replacement strain relief added |
| No `Lighting_Keepout` component or body exists | PASS — absent from browser, assembly STEP and pack |
| Rear wall thickness = `rear_light_shield_t` | PASS — 1.20 mm at all 11 probes, both tools |
| Rear wall confined to the OLED bay | PASS — nothing above y +20.50 in its Z band but the pedestals |
| Only penetration is the four-pin slot | PASS — 45.024 mm³ measured against 45.024 mm³ required |
| Rear wall clear of the PCB and components | PASS — 4.10 mm behind DATUM B |
| Sprung posts, pedestals, pads, reliefs, root fillets retained | PASS — full Ø8.60 / Ø6.00 / Ø4.80 at both |
| Side uprights, fixing arms/bosses, opposite rail retained | PASS |
| Uprights terminated with deliberate printable radii | PASS — R1.80 half-round caps |
| One connected open-ended solid | PASS — 1 lump in Fusion, 1 connected component on the mesh |
| M2 heat-set architecture completely removed | PASS — no bore, depth, recess, chamfer, backing or BOM entry |
| Named original-nut parameters created | PASS — §12.2 |
| 3.80 mm across-flats reading recorded, then **confirmed** | PASS — §12.2; confirmed 2026-08-30, now a measured value |
| Hex pocket, seat, head-seat depth, envelope, boss wall, captive retention | PASS — §12.4 |
| Original load path, no clamp through glass or PCB | PASS — §12.5 |
| 49.00 mm pitch unchanged | PASS — 49.00000 mm exactly |
| Rear wall is integral, one solid with the carrier | PASS — 1 lump, no separate cover component |
| Rear wall built forward from the existing rear plane | PASS — external envelope unchanged at 8.00 mm deep |
| Rear wall does not re-enter the deleted rail region | PASS — stops at y +20.50, old band still empty |
| Four-pin opening = header envelope + named clearances | PASS — 11.20 × 3.35 from 10.00 × 3.00 + 0.60/0.60 |
| Front insertion and removal sweeps still clear | PASS — glass, tips and header corridors CLEAR |
| Fixed datum and snap-retention results unchanged | PASS — identical to the Rev P.2 figures |
| OLED-to-Perspex gap unchanged | PASS — 0.30 mm |
| Nut pockets, captive retention, service removal unchanged | PASS — §12.4 |
| Original bolts do not bottom | PASS — 5.00 mm grip, 15.00 mm ceiling, both reported open |
| No thin slivers or unsupported critical geometry | PASS — 0 faces < 0.02 mm², 0 edges < 0.05 mm |
| Rear-face-down print orientation still suitable | PASS — the wall is the first 6 layers, bed-supported |
| Four sprung-post bodies exist, one per mounting hole | PASS — 4 of 4, both tools |
| Four split slots exist | PASS — 4 of 4 measured at 1.20 mm off the mesh |
| Four positive retaining noses exist | PASS — 4 of 4 measured at Ø3.20 ahead of the PCB front face |
| No plain-post body or parameter remains | PASS — a plain post has neither split nor barb; all four have both |
| All four posts concentric with the transformed holes | PASS — shafts measured Ø2.79 in Ø3.00 at all four |
| All four hooks: positive overlap and axial clearance | PASS — 0.100 mm radial, 0.10 mm axial, all four |
| Combined insertion force does not bow the PCB | PASS — 28.6 N, 0.057 mm worst-case bow < 0.10 mm hook clearance |
| All four roots connected and printable in the 6.00 mm carrier | PASS — 1.30 mm floor, R0.80 fillet intact, 0 slivers |
| Rear shield and connector light blocks intact | PASS — 1.20 mm everywhere, blocks tied into both pedestals |
| PCB can be deliberately released and withdrawn | PASS — §14.5, row at a time, 1.41° pivot inside a 7.13° allowance |
| Carrier depth exactly 6.00 mm | PASS — measured on the solid and the mesh |
| Finished pin opening 14.00 × 4.19 mm | PASS — measured both ways |
| One consistent 180° transform; connector at the bottom | PASS — header envelope entirely below the active centre |
| Active area horizontally centred | PASS — centre x 0.0000 mm |
| ~~Active-area bottom edge on the opening bottom~~ | **SUPERSEDED by §17 — check deleted, not softened** |
| Fixing centres moved exactly `carrier_fix_y_from_previous` | PASS — −7.00 mm relative to the OLED group, both tools |
| Active area exactly 7.00 mm higher than the superseded datum | PASS — centre y +6.7000, measured on the built body |
| Both bolt bores on one centreline, 49.00000 mm pitch, no skew | PASS — measured off the mesh at y 0.0000 |
| Connector cut-out side is unambiguously the bottom | PASS — rail cut and pin opening both at y −13.80 |
| Moved arms continuously joined, no neck or sliver | PASS — 2.00 mm overlap, 0 / 0 slivers |
| Hard stops, nut pockets and clamp path intact after the move | PASS — §17.4 |
| **Visible active-area extent through the opening** | **REPORTED, not passed — 8.30 mm of 14.70 mm visible, 6.40 mm above the opening. §17.3** |
| Panel-fixed holes not moved with the OLED | PASS — y 0.00, 49.00000 mm pitch |
| **Bonded-glass boundary at all four holes** | **BLOCKED — §14.4. THE Rev P.5 print gate** |
| **Lighting-unit position** | **NOT MODELLED AND NOT MEASURED — §11.5. CAD makes no clearance claim** |
| **Light leakage** | **NOT MEASURED — powered test §12.22 gates release** |
| **Nut across-corners, bolt length, pocket fit** | **NOT MEASURED — §12.6** |

**Amendment approved for CAD**, with the measurement items above gating the
print and the brief §12 tests — including the installed lighting-unit clearance
test §12.14 and the powered light-leak test §12.22 — gating release.
