LeweeLewee/Decca/mechanical/Drawings/Decca_OLED_Display_Mount_CAD_Review_revO.md

# Decca OLED Display Mount — CAD Redesign Specification (Rev O / Rev P correction)

Supersedes Rev N as the active design direction for the OLED carrier.

Amended 2026-08-29 after the physical Rev P prototype failed loose-carrier
retention. Rev P remains an open prototype revision; this correction supersedes
the rear-insertion and friction-retention clauses below as originally issued.

Amended again 2026-08-29 after the corrected Rev P.2 prototype successfully
retained the OLED and achieved the intended Perspex tolerances. The remaining
integration failure is a collision between the carrier end rail / cable-tie
projection below the sprung-post pair as installed and the original Decca
lighting unit, which cannot be removed. The lighting unit is now a mandatory
physical clearance interface and Rev P remains open for this bounded correction.

Amended again 2026-08-29 after confirming that the original Decca front bolts
use a non-standard thread. The M2 heat-set inserts and replacement M2 screws are
deleted from the design. The original bolts and their original matching
six-sided nuts shall be reused at the unchanged 49.00 mm fixing pitch.

Amended again 2026-08-29 after review of Rev P.3. Delete the newly introduced
synthetic `Lighting_Keepout` / `REF_Lighting_Keepout` CAD component: it is not a
measured physical part and is not required in the assembly. Preserve the proven
lighting-unit clearance by keeping the colliding lower end rail deleted. Close
the rear of the OLED bay with an integral opaque carrier wall to prevent the
cabinet LEDs washing light around the OLED, leaving only the minimum opening
required for the four input/header pins and their wiring.

Amended again 2026-08-29 after physical packaging review of Rev P.4. Reduce the
plastic carrier depth from 8.00 to **6.00 mm**; enlarge the finished four-pin
opening by 25% in both axes from 11.20 × 3.35 mm to **14.00 × 4.19 mm**; add two
integral internal light-block walls beside that opening without exceeding the
revised carrier/back-plate envelope; and correct the vertical datum. The OLED
shall be rotated in plane so the four-pin side is at the bottom, and the bottom
edge of its visible active area shall align with the bottom edge of the measured
Perspex opening. The original Perspex holes remain fixed physical interfaces.

Amended again 2026-08-29 to replace the remaining two non-sprung locating posts.
Rev P.5 shall use **four sprung locating-and-retaining posts**, one in every PCB
mounting hole. No plain post remains. The newly converted pair requires the same
positive retention proof as the existing pair plus direct bonded-glass clearance,
combined insertion-force, PCB-bow, root-strength and four-post release evidence.

Amended again 2026-08-29 to correct the mounting-point vertical offset. With the
open connector-cut-out side defined as the carrier bottom, move both carrier
fixing centres **7.00 mm downward** relative to the OLED bay. The original
Perspex holes remain untouched; aligning the revised carrier to them raises the
screen by 7.00 mm relative to the Perspex opening. This supersedes the earlier
active-area-bottom-to-opening-bottom alignment rule.

Platform: Autodesk Fusion 360. Manufacture: FDM 3D print.

## 1. Reason for redesign

Physical print-and-fit iterations of Rev N showed that the front-loaded architecture had become constrained by OLED depth. Rev O changes the topology rather than further tuning the Rev N front plate and retainer arrangement.

The governing design objective is to place the OLED glass close to the inside
face of the original Perspex while keeping all front-fastener preload out of the
OLED glass and PCB.

The subsequent Rev P prototype exposed a second architectural error. Rev P
inserted the OLED from the rear towards the Perspex, but placed its nominal PCB
datum shoulders behind the PCB rear face. Those shoulders restrained withdrawal
in the opposite direction; forward handling retention relied only on four
0.10 mm edge-friction contacts. The physical screen passed through the loose
carrier. This physical result invalidates the analytical friction-hold release
claim and is the governing evidence for the correction in this document.

The corrected Rev P.2 post-and-datum architecture subsequently passed physical
fit testing: screen retention and the Perspex tolerance are satisfactory. That
test also exposed an installation-envelope omission. The transverse carrier
rail and integral cable-tie projection on the lighting-unit side collide with
the retained original Decca lighting assembly. The radio-side interface, rather
than OLED geometry, now governs the next correction.

Rev P.3 then represented the unmeasured lighting-unit clearance as a large new
reference component. That body is not controlled by physical measurements and
shall not remain in the Fusion assembly, exports, drawings or verification
model. The installed fit test remains the authority for lighting-unit clearance.
The cabinet lighting also creates a credible optical leakage path around the
rear and edges of the OLED; the carrier itself shall therefore provide the
light barrier.

## 2. Corrected Rev P architecture — mandatory topology

The OLED module shall load into the loose carrier from its
**flush/Perspex-contact side**, moving rearwards onto fixed PCB datum pads.

The carrier shall sit behind the OLED PCB. The OLED glass/display projects forwards towards the inside face of the Perspex.

**No carrier front plate, seating land, shoulder, lip or other structural load
feature may occupy the space between the front face of the OLED PCB and the
Perspex.** This continues to reject the failed Rev O implementation that
recreated the Rev N 1.10 mm forward retention plane as short seating lands.

A narrowly controlled exception is permitted only for local sprung-post noses
inside verified PCB mounting-hole keep-outs. A snap nose may cross the PCB front
plane only as far as required for positive handling retention and only when its
clearance to the OLED glass, solder joints, Perspex and full assembly path is
demonstrated. It shall not establish OLED depth or carry front-fastener preload.

The loose carrier shall positively constrain the PCB in both axial directions:

1. fixed, non-spring datum pads acting on rear-safe PCB areas stop rearward
   insertion and establish OLED Z position; and
2. sprung locating-post noses provide positive forward retention after seating,
   with deliberate axial clearance so they retain rather than clamp the PCB.

Friction, gravity or the assumed elastic modulus of printed material shall not
be used as the primary proof of axial retention. The Perspex remains redundant
final containment after assembly, but the OLED must not fall through or fall
away from the loose carrier during handling.

The carrier/Perspex assembly therefore performs two independent functions:

1. **Structural load path:** original Decca bolt and matching nut → carrier
   structural bosses / hard stops → Perspex.
2. **OLED location and capture:** fixed rear PCB datum pads establish depth;
   locating posts establish X/Y; sprung post noses retain the loose module;
   Perspex provides redundant forward containment after assembly.

The glass must never be the structural compression stop.

## 3. Existing Decca interface — measured values are authoritative

Use the measured and print-confirmed dimensions already recorded in the repository, not the superseded Spec v1.0 values:

- Original Perspex thickness: 3.00 mm.
- Existing aperture: **35.20 mm W × 15.30 mm H**.
- Existing fixing-hole pitch: **49.00 mm horizontal**.
- Existing fixing-hole vertical position: controlled by the physical Perspex
  holes, independently of the OLED active-area centre. Do not move or redrill
  the Perspex and do not derive carrier-hole Y from screen centring.
- No additional holes, cutting or irreversible modification to the original Perspex.
- The original Decca bolts enter from the front of the Perspex and fasten into
  their original matching nuts captured by the rear carrier.
- The original bolt thread is non-standard. Do not substitute M2 screws, M2
  heat-set inserts or any inferred standard thread.

If any later physical measurement contradicts these values, the physical measurement wins and the parameter is updated explicitly.

## 4. Front bezel

The front bezel remains a separate cosmetic trim around the aperture only.

It must not include the original fixing holes and must not carry structural
load. Retain the validated Rev N bezel unless physical testing identifies a
specific reason to change it.

## 5. OLED loading, datum and retention

### 5.1 Flush-side loading

The OLED PCB shall insert from the carrier's flush/Perspex-contact side by a
controlled rearward translation. The glass enters the central clearance first;
the PCB rear face then seats on fixed rear datum pads. The carrier shall retain
clearance around the header and solder joints after seating. Rear access is now
limited to the local four-pin/header opening specified in §8.3.

### 5.2 Fixed positive OLED Z datum from behind

OLED fore/aft position shall be established by **rear PCB support lands / shoulders acting on the rear face or rear-safe areas of the PCB**.

These support features shall be rigid parts of the carrier body, not faces on a
moving spring. They stop rearward insertion, locate the PCB in Z and must not
project ahead of the PCB front face.

The intended section is therefore:

```text
Perspex
  |
small controlled optical gap
  |
OLED glass
  |
OLED PCB
  ^
rear PCB support lands / datum
  |
rear carrier
```

Separate carrier structural bosses / hard stops shall contact the Perspex
directly outside the OLED module envelope and carry the original-fastener preload.

### 5.3 Locating and retaining posts

Use four split sprung locating-and-retaining posts, one at each PCB mounting
hole. Delete both plain-post bodies, plain-post parameters and plain-root-relief
geometry. Each post shall provide X/Y location and positive forward retention.

Candidate starting geometry from the earlier printed-post development is a
2.80 mm sprung shaft, 0.70 mm split slot, 3.20 mm initial barb diameter and
R0.80 root fillet. These are prototype inputs, not automatic acceptance values.
The two already proven sprung posts may retain their validated local geometry if
the complete Rev P.5 regeneration confirms it. The newly converted pair may use
separately named sprung geometry where its measured glass envelope or the new
6.00 mm carrier depth requires a smaller nose, different split orientation or
revised root relief. It must remain sprung; do not silently revert it to a plain
post.

Before print release, measure the actual bonded-glass boundary relative to all
four mounting holes. Every sprung shaft, split, lead-in and retaining nose shall
remain inside the verified hole keep-out and clear of the bonded glass throughout
insertion, seating, retention, deliberate release and withdrawal. Rev K's narrow
pair depended on only 0.20 mm assumed glass clearance; that assumption is not
evidence for Rev P.5.

Design intent:

- locate the PCB consistently in X/Y;
- prevent the loose OLED falling away during handling and installation;
- prevent the seated OLED translating forwards through the loose carrier by
  positive geometric overlap, not edge friction;
- avoid significant PCB bending or insertion force;
- keep sprung noses inside verified mounting-hole keep-outs and clear of bonded
  glass throughout insertion, seating and removal;
- limit the combined force from all four posts so the PCB can seat without bowing
  and without using the Perspex, glass or rear wall as an insertion reaction;
- provide axial clearance between each engaged nose and the PCB so the post does
  not clamp the module; and
- provide an identified, accessible release sequence for all four posts after
  the carrier is removed from the Perspex, with the closed rear wall present.

A full swept insertion/removal corridor check is mandatory before print release.

### 5.4 Retainer bar

Delete the separate retainer bar from Rev O and retain a two-printed-part system:
carrier plus the existing bezel.

The post-and-datum system provides positive loose-carrier retention. The
assembled Perspex provides redundant final containment without becoming the OLED
depth datum or applying preload to the glass.

## 6. Optical depth and glass protection

Target nominal glass-to-Perspex gap: **0.15–0.30 mm**.

Select the final nominal from measured OLED geometry and realistic FDM tolerance. A nominal around 0.30 mm is acceptable if required for robustness.

Critical requirements:

- the OLED glass must not become the structural stop when the original bolts are tightened;
- tightening the original bolts must not alter OLED depth;
- there shall be no carrier material between the OLED PCB front face and Perspex used to establish this gap.

## 7. Solder-tip constraint — resolved by module preparation

The physical OLED solder tips project more than 2 mm from the PCB front face. The
Rev P depth chain proved that the earlier 1.50 mm preparation limit is
incompatible with the 0.30 mm optical gap. Prepare all display-side protrusions
to a **maximum of 1.00 mm proud**.

This is an accepted assembly preparation step and shall be treated as the design input for the corrected Rev P prototype.

Accordingly:

- model `oled_tip_proud = 1.00 mm maximum`;
- provide sufficient local carrier clearance around the solder joints and header;
- do not redesign the carrier topology merely to accommodate untrimmed >2 mm tips;
- verify that the prepared 1.00 mm tips do not interfere with the Perspex or any carrier feature in the final assembly or insertion path.

The hard geometric ceiling is the measured glass proud plus the selected optical
gap. Preserve at least 0.10 mm clearance to the Perspex rather than aiming at the
zero-clearance ceiling.

## 8. Carrier structural design

Rev O should restore sensible FDM section thicknesses behind and around the OLED module.

Guidance:

- approximately 2.0–3.0 mm structural wall thickness where geometry allows;
- reinforce the two original-fastener boss regions appropriately;
- use direct carrier-to-Perspex hard stops outside the OLED module envelope;
- avoid unnecessary thin membranes around the display window;
- leave the local four-pin/header access and internal component clearance
  specified in §8.3;
- maintain cable/header clearance and serviceability;
- minimise part count and avoid a separate retainer.

### 8.1 Original Decca lighting-unit clearance — no keepout component

The original Decca lighting unit is retained and cannot be removed. The carrier
shall therefore be open on the lighting-unit side below/outboard of the sprung
locating-post pair as the part is installed in the radio.

Do not create or retain a separate `Lighting_Keepout`,
`REF_Lighting_Keepout`, `LIGHTING_UNIT_KEEPOUT` or equivalent proxy component,
body or exported part. Its geometry was asserted rather than measured and would
misrepresent the physical assembly. Demonstrate this interface through the
installed physical clearance test, supported by direct measurements if later
available.

Delete the complete continuous end rail in that region, including the central
integral cable-tie / strain-relief projection and its slots. Do not merely thin,
notch or shorten the rail: no bridge may remain across the two side uprights
inside the lighting-unit keep-out.

The removal boundary shall preserve:

- both connector-side sprung posts, their full pedestals, datum pads, reliefs
  and filleted roots;
- the local pedestal-to-side-upright connections;
- both vertical side uprights and both 49.00 mm fixing-boss/load paths;
- the opposite transverse rail; and
- the OLED insertion, removal and wiring corridors.

Terminate the two side uprights with intentional radii or fillets adjacent to
the retained pedestal roots. Do not leave thin remnants, sharp internal corners
or tangent-only connections. The lighting keep-out takes precedence over an
integral cable-tie feature; any replacement strain relief must be placed outside
the keep-out and must have separately demonstrated radio-side clearance.

### 8.2 Original Decca bolt and captive-nut interface

Reuse the two original Decca front bolts and their two original matching nuts.
Their thread is non-standard and is controlled by the physical original parts,
not by an M2 or other catalogue-thread assumption. Delete the M2 heat-set insert
bores, insert chamfers, insert backing dimensions and replacement M2 screws from
the carrier and manufacturing pack.

The measured nut envelope is:

- six-sided head/profile;
- **3.80 mm measured width**;
- **1.40 mm axial head-seat / countersink depth**; and
- **10.00 mm total nut length**.

For the first corrected CAD model, interpret the reported 3.80 mm width as the
distance across opposite flat faces. Expose that interpretation explicitly as a
named parameter and drawing note; do not derive it from an assumed standard nut.
Before release, verify the physical part across flats and across corners. If the
3.80 mm measurement proves to be across corners instead, update the single named
parameter and regenerate the pocket before printing.

Provide a rear-accessible, regular-hex anti-rotation pocket and an axial seating
shoulder for each original nut. The 1.40 mm head-seat depth shall be positively
defined; it shall not depend on the nut crushing into printed material. Provide
a continuous clearance envelope for the full 10.00 mm nut length and the engaged
bolt, including insertion and removal. The nut may not bottom before the carrier
seats against the Perspex, be pulled through the boss under tightening, rotate
in its pocket, contact the OLED/PCB/wiring, or enter the original lighting-unit
keep-out.

The nut shall also remain captive when the loose carrier is inverted and offered
into the radio before either bolt is engaged. Use a documented, serviceable
retention lip, small snap or validated controlled fit; do not use permanent
adhesive. Handling retention is separate from the axial seating shoulder and
shall not be credited as part of the structural clamp-load path.

Use separate named parameters for the measured nut width, pocket fit allowance,
head-seat depth and total nut length. Pocket clearance is a print-process fit
allowance, not permission to alter the 3.80 mm physical-part measurement. Where
that fit has not already been demonstrated on the selected printer/material,
release a small hex-pocket fit coupon before the full carrier and record the
selected allowance.

The carrier-to-Perspex hard-stop face remains the structural datum. The nut
pocket shall be concentric with each existing fixing centre, preserve the exact
49.00 mm centre pitch and leave a continuous, measurable boss wall around the
hex envelope. The original load path is: bolt head → Perspex → carrier seating
face / hard stop → captive original nut → original bolt thread. No part of this
load path may pass through the OLED glass or PCB.

### 8.3 Integral rear light shield

Close the rear of the OLED module bay with a continuous wall formed integrally
with the carrier. This wall replaces the current open rear window; it is not a
separate cover or component. Its purpose is to block direct and reflected light
from the Decca cabinet LEDs from reaching the rear and edges of the OLED or
producing a visible glow through the Perspex aperture.

The rear wall shall:

- span the OLED bay and join continuously to the retained carrier frame;
- use a named `rear_light_shield_t` parameter; for a 0.40 mm nozzle the first
  prototype shall start at 1.20 mm or three actual extrusion widths, whichever
  is greater;
- be printed as solid opaque material, not as exposed sparse infill or a thin
  translucent membrane;
- use opaque black material for the prototype and final part unless an
  alternative is physically shown to block the installed lighting;
- remain behind and clear of the complete seated PCB/component envelope;
- not become the OLED Z datum, touch or preload the PCB, or alter the validated
  rear datum pads and Perspex gap;
- preserve front-side OLED insertion, positive sprung-post retention and the
  deliberate service-release path;
- preserve the open lighting-unit-side rail deletion required by §8.1; and
- remain one connected printable solid with the carrier.

The rear wall may bridge the side uprights only across the OLED bay itself. It
shall terminate within that bay and shall not extend into or recreate the
deleted end-rail/cable-tie region below/outboard of the sprung-post pair.

Provide only one local rear opening: the minimum practical aperture for the
OLED's four input/header pins and their attached conductors. Size that opening
from the actual four-pin envelope plus documented print and wiring clearance;
do not retain a general rear window. Keep the opening close-fitting and local to
the header so it does not become a direct light path. A short integral hood or
offset around the pin opening is permitted only if needed after the powered
light-leak test and only if it clears the connector, wire bend and original
lighting unit; do not add another printed component.

The closed cavity shall not trap the module permanently. The CAD build review
must identify how the sprung posts are deliberately released and the OLED is
withdrawn from the front with the rear wall present.

### 8.4 Rev P.5 packaging and vertical-datum correction

#### Carrier depth

Reduce the carrier's plastic Z envelope by exactly 2.00 mm:

- Rev P.4 carrier depth: 8.00 mm;
- Rev P.5 carrier depth: **6.00 mm** measured from the Perspex seating plane to
  the carrier rear plane; and
- retain `rear_light_shield_t = 1.20 mm` unless the actual extrusion-width rule
  in §8.3 requires a greater value.

The project owner confirms that the resulting nominal space behind the seated
screen is available. The CAD shall nevertheless recalculate the shield-to-PCB,
header, sprung-post relief, pedestal-root, nut-pocket and wiring clearances from
the finished 6.00 mm geometry. Do not truncate a root relief, fillet, nut seat or
connector envelope merely to meet the external depth.

#### Four-pin opening and internal light blocks

The Rev P.4 finished four-pin opening is 11.20 × 3.35 mm. Increase both finished
linear dimensions by 25%:

- width: **14.00 mm**;
- height: **4.19 mm** nominal (4.1875 mm unrounded); and
- centre the opening on the transformed four-pin/header envelope.

This explicit finished size supersedes the earlier minimum-opening instruction.
Keep the opening local; do not reopen the general rear window.

Add two integral opaque light-block walls, one immediately to each lateral side
of the four-pin opening. The walls shall form a short internal tunnel beside the
pins, extending forward from the inside face of the rear shield while remaining
clear of the header, conductors, wire bend and OLED insertion/removal sweep.
Each wall shall be at least three actual extrusion widths thick and shall join
the rear shield as part of the same carrier solid.

Neither light-block wall may extend behind the revised carrier rear plane,
outside the existing back-plate X/Y footprint, into the deleted end-rail region,
or beyond the **6.00 mm** overall carrier envelope. They are internal baffles,
not external fins and not separate components.

#### Screen and fixing-hole vertical datum

Define the open side containing the four-pin connector cut-out as the carrier
**bottom** (`-Y`). Retain the complete 180-degree in-plane OLED transform so the
four-pin/header side is also at the bottom. PCB, glass, active area, four mounting
holes, header, solder tips, datum pads, posts, pocket, rear-wall opening and light
blocks shall remain one internally consistent OLED-dependent group.

Move both carrier fixing centres, their bosses, bores, captive-nut pockets and
structural arms exactly **7.00 mm toward the carrier bottom** relative to that
OLED-dependent group. Provide one named parameter:

`carrier_fix_y_from_previous = -7.00 mm`.

Both fixing centres shall remain on one common horizontal centreline and retain
the exact 49.00 mm X pitch. The shift is vertical only; no relative X movement,
skew or pitch change is permitted.

The original Perspex and its holes are not moved, redrilled or redefined. In the
assembled reference, the carrier fixing holes shall coincide with the physical
Perspex holes. Therefore the equivalent panel-coordinate implementation is to
raise the OLED bay and all OLED-dependent carrier geometry by **+7.00 mm** while
leaving the panel holes fixed. Do not create a Fusion assembly in which the
carrier holes and Perspex holes are shown 7.00 mm apart.

This instruction supersedes the earlier rule that aligned the visible active-area
bottom edge with the Perspex opening bottom. Using the immediately preceding
Rev P.5 datum as the numerical baseline, the expected modelled active-area centre
moves from `y = -0.30 mm` to **`y = +6.70 mm`**, with predicted edges at
`y = -0.65 mm` and `y = +14.05 mm`. These figures are a transform cross-check,
not proof that the visible position is acceptable. Record the actual powered
screen position through the Perspex and obtain physical fit evidence before
release.

## 9. Required corrective CAD changes for open Rev P

1. Replace rear insertion with flush/Perspex-side insertion moving rearwards.
2. Replace the moving Rev P edge-finger shoulders with fixed, non-spring rear
   PCB datum pads.
3. Delete the four PCB-edge friction fingers, their tongues, shoulders and
   radial prise holes.
4. Add four sprung locating-and-retaining posts as specified in §5.3, providing
   positive forward retention at every PCB mounting hole after the PCB seats.
5. Keep all structural PCB datum geometry behind the PCB front face; permit only
   verified local snap noses to cross that plane inside mounting-hole keep-outs.
6. Provide a clear path for the OLED glass with no forward PCB seating lands.
7. Retain separate positive carrier-to-Perspex hard-stop geometry to carry the
   original-fastener preload.
8. Delete the separate retainer bar.
9. Model display-side protrusions at 1.00 mm maximum after preparation.
10. Use the measured 49.00 mm fixing pitch and 35.20 × 15.30 mm aperture.
11. Retain the existing bezel unless new test evidence requires a change.
12. Preserve horizontal active-area centring; set the vertical screen position
    from the 7.00 mm downward carrier-fixing-centre offset specified in §8.4.
13. Keep the design fully parametric in Fusion 360.
14. Remove the complete lighting-unit-side end rail and integral cable-tie
    projection as specified in §8.1, while retaining the post pedestals and side
    uprights as one connected solid.
15. Keep Rev P open until the modified carrier has passed both the retained OLED
    checks and an installed clearance test against the non-removable lighting unit.
16. Delete both M2 heat-set insert interfaces and replace them with the captive
    original-nut interface specified in §8.2; do not change fixing centres.
17. Retain the original non-standard-thread bolts and matching nuts as controlled
    physical parts; do not add replacement M2 hardware to the BOM.
18. Delete the synthetic lighting-unit keepout component/body and remove it from
    the Fusion assembly, generator, verification model, drawings and exports.
19. Close the OLED bay with the integral opaque rear wall specified in §8.3,
    leaving only the local four-pin/header opening.
20. Apply all four Rev P.5 packaging corrections in §8.4 as one controlled datum
    update; do not move the original Perspex or its existing fixing holes.
21. Convert the remaining two plain posts to sprung posts and delete all plain-post
    geometry and parameters; validate the complete four-post system.
22. Define the connector-cut-out side as bottom and move both carrier fixing
    points 7.00 mm toward that bottom relative to the complete OLED-dependent
    geometry, without moving the original Perspex holes or changing 49.00 mm pitch.

## 10. Mandatory CAD validation gate

Before the corrected Rev P geometry is accepted for a prototype print, verify all of the following on the actual generated geometry:

- carrier × Perspex: clear except intended structural seating faces;
- no structural carrier geometry ahead of the OLED PCB front face within the
  OLED module envelope, except verified local snap noses in mounting-hole keep-outs;
- rear PCB support contacts only intended PCB support areas;
- carrier × OLED glass: clear throughout insertion, seating and removal;
- carrier × OLED PCB: correct fixed rear datum, X/Y location and controlled
  positive snap overlap;
- carrier × header and prepared 1.00 mm solder joints: clear;
- prepared solder joints × Perspex: at least 0.10 mm clear;
- OLED glass × Perspex: 0.15–0.30 mm nominal gap;
- original-fastener load path terminates through carrier hard stops into
  Perspex, not OLED glass or PCB;
- snap features locate and positively retain the PCB without excessive strain,
  bending or axial preload;
- rearward PCB translation stops on fixed datums and forward PCB translation is
  blocked by positive snap geometry without relying on friction;
- OLED can be inserted from the flush side and removed through an identified
  release path without bonded glass sweeping through a rigid barb/post envelope;
- carrier seats flat against Perspex;
- no synthetic lighting-unit keepout component or body exists in the Fusion
  assembly, browser, generator output, STEP assembly or manufacturing pack;
- installed physical clearance to the retained Decca lighting unit is preserved,
  including the former rail and cable-tie region;
- there is no continuous carrier bridge across the lighting-unit side below or
  outboard of the sprung-post pedestals;
- the two connector-side sprung-post pedestals retain their required datum area,
  relief depth, root fillets and connection to the side uprights after the rail cut;
- the remaining U-shaped frame, fixing arms and opposite rail form one closed solid
  with no slivers or tangent-only joins;
- removal of the end rail does not change the 49.00 mm fixing pitch, OLED Z chain,
  post positions, snap overlap, PCB datum contact or Perspex seating plane;
- the remaining seating faces resist rocking when the two original bolts are snug;
- each original nut fits its six-sided pocket with positive anti-rotation and a
  defined axial seat, and can be installed and removed from the rear;
- each original nut remains captive when the loose carrier is inverted and
  offered into the radio before either bolt is installed;
- the full 10.00 mm nut and engaged original bolt clear the OLED, PCB, wiring,
  Perspex optical aperture and retained lighting-unit keep-out;
- neither original bolt bottoms in its nut nor pulls the nut through the carrier
  before the carrier hard stops seat against the Perspex;
- the two nut pockets remain concentric at exactly 49.00 mm pitch and retain a
  continuous structural boss wall;
- the rear OLED bay is closed by one continuous integral solid wall, with no
  open rear window or separate rear-cover component;
- the only rear-wall penetration is the local four-pin/header opening and it is
  no larger than required by the measured pin, connector and wiring envelope;
- the rear wall clears every seated PCB component, does not contact the PCB and
  does not change the fixed datum, snap engagement, release path or optical gap;
- the selected wall thickness and opaque black print produce no visible light
  transmission or edge glow under the installed cabinet lighting;
- carrier depth from Perspex seating plane to rear plane is exactly 6.00 mm;
- shortening the carrier leaves valid sprung-post reliefs, pedestal roots,
  fillets, nut seats and a positive rear-wall-to-PCB/component clearance;
- all four PCB mounting holes contain sprung locating-and-retaining posts and no
  plain-post body, parameter, probe or report entry remains;
- every sprung nose remains inside its measured mounting-hole/glass keep-out and
  clears bonded glass through insertion, seating, retention, release and removal;
- individual and combined four-post insertion forces and worst-case strains are
  reported, remain within the selected material/process limits and do not bow the PCB;
- all four hooks show positive geometric overlap with deliberate axial clearance,
  and the documented four-post release sequence is accessible with the rear wall present;
- the finished four-pin opening measures 14.00 × 4.19 mm and remains centred on
  the transformed connector envelope;
- two integral light-block walls exist beside the opening, remain inside the
  back-plate X/Y footprint and 6.00 mm Z envelope, and clear the pins, wires and
  insertion/removal sweep;
- the complete OLED reference and OLED-dependent carrier geometry have undergone
  one consistent 180-degree in-plane transform, placing the connector at the bottom;
- the connector-cut-out side is unambiguously the carrier bottom and both fixing
  centres are exactly 7.00 mm farther toward that bottom than in the preceding
  Rev P.5 geometry, measured relative to the OLED-dependent group;
- the visible active area remains horizontally centred and is exactly 7.00 mm
  higher relative to the Perspex opening than in the preceding Rev P.5 datum;
- the model reports the resulting visible active-area extent through the Perspex
  and does not retain the superseded bottom-edge-alignment PASS check;
- the panel-fixed boss/hole centres remain coincident with the existing Perspex
  holes at exactly 49.00 mm horizontal pitch and are not moved with the OLED;
- both shifted fixing arms remain continuously joined to the 6.00 mm carrier,
  clear the OLED bay, rear shield, light blocks and lighting-unit installation
  path, and carry clamp load through the existing hard stops;
- no unprintable thin slivers or unsupported critical features;
- normal FDM wall thickness is restored in structural areas.

**A static final-position interference check is insufficient. Swept insertion
and removal checks, plus a directionally correct positive-retention check, are
mandatory. A friction-versus-module-weight calculation cannot satisfy the
positive-retention requirement.**

## 11. Design-review gate before Fusion build

Before generating the next Fusion model, produce and review a simple side-section / topology diagram showing:

- Perspex;
- optical gap;
- OLED glass;
- PCB;
- rear PCB support datum;
- structural carrier hard stops to Perspex;
- original-bolt/captive-nut load path;
- all four sprung locating-and-retaining posts;
- local positive snap overlap on the PCB front face; and
- the flush-side insertion direction;
- the integral rear light-shield wall; and
- the 6.00 mm carrier rear plane;
- the 14.00 × 4.19 mm four-pin/header opening and wire-exit path;
- the two internal light-block walls; and
- the connector-cut-out side identified as bottom, with the two fixing points
  dimensioned 7.00 mm downward relative to the OLED group and coincident with
  the unchanged Perspex holes in the assembled view.

The CAD build must not proceed unless the section shows positive stops in both
axial directions: fixed rear datum pads stopping insertion and sprung noses
stopping forward escape. It must contain no carrier land, plate or structural
shoulder between the PCB front face and Perspex. Only the controlled local snap
nose exception in §2 is permitted.

## 12. Prototype acceptance tests

The next corrected Rev P print is a geometry-and-retention prototype. Check in
this order:

1. flush-side rearward insertion of the OLED without glass or component contact;
2. PCB rear face seats consistently on every fixed datum pad;
3. all four sprung posts engage with visible positive overlap and no PCB bow;
4. the loose carrier retains the OLED when inverted in every axis and during a
   gentle handling shake, with no fall-through or fall-away;
5. the stated release method removes the OLED without damaging posts or PCB;
6. carrier seats flat against Perspex;
7. actual OLED-to-Perspex gap;
8. powered active-area position after the 7.00 mm mounting-offset correction:
   horizontally centred and visibly raised by 7.00 mm relative to the preceding
   Rev P.5 position; record the visible active-area edges through the opening;
9. bezel alignment;
10. tightening the original Decca bolts does not change OLED depth or stress the module;
11. prepared solder joints and header clear the Perspex and carrier;
12. no rattle when assembled; and
13. no separate retainer is required;
14. the carrier clears the original lighting unit throughout offering-up,
    seating and removal, with the lighting unit left in place;
15. the open-ended carrier shows no perceptible lateral rack or twist when
    handled and when the two original bolts are snug; and
16. the OLED retention, removal and gap remain unchanged after removal of the
    end rail, while the intentional §8.4 vertical alignment is achieved;
17. both original nuts seat fully in their hex pockets without rotation, cracking
    or excessive insertion force, remain captive with the loose carrier inverted,
    and can still be deliberately removed for service;
18. both original non-standard-thread bolts engage freely, do not bottom, and
    clamp the carrier hard stops to the Perspex; and
19. the captive-nut installation and engaged fasteners remain clear of the
    original lighting unit throughout offering-up, seating and removal;
20. no synthetic lighting-unit keepout component or proxy body remains in the
    Fusion design, assembly export or manufacturing pack;
21. the closed rear wall clears the PCB and four-pin connection, does not alter
    insertion, retention, release or OLED-to-Perspex gap, and has no unintended
    rear opening; and
22. with the OLED powered through black, dim and normal display content and the
    Decca cabinet LEDs operated through their usable brightness range, no visible
    rear-light glow, edge leakage or contrast washout appears through the Perspex
    aperture in representative room lighting;
23. the carrier measures 6.00 mm from Perspex seating plane to rear plane and
    still seats without contact behind the screen;
24. the connector opening measures 14.00 × 4.19 mm and the pins, conductors and
    wire bend pass freely;
25. both internal light-block walls remain within the back-plate footprint and
    carrier-depth envelope and show no pin/wire contact;
26. the open four-pin side is physically at the bottom and both carrier fixing
    centres are 7.00 mm down relative to the OLED-dependent geometry;
27. both shifted carrier fixing holes align with the untouched Perspex holes,
    retaining exactly 49.00 mm horizontal pitch, and the resulting screen is
    7.00 mm higher relative to the opening than the preceding Rev P.5 datum; and
28. all four sprung posts seat, retain and deliberately release the PCB without
    bonded-glass contact, excessive insertion force, permanent post set, root
    cracking or PCB bow; no plain post remains.

CAD and mesh checks may release this prototype print, but they shall not close
the retention finding. Physical tests 1–5 are mandatory before Rev P can regain
a release recommendation.

The project owner reports that the corrected Rev P.2 prototype has satisfied the
retention and Perspex-tolerance intent. Treat that as submitted physical evidence,
not as permission to skip regression testing after the lighting-clearance cut.

## 13. Design decision

Rev N should receive no further architecture-level iteration.

The failed first Rev O implementation is rejected because it recreated the critical Rev N geometry as **1.10 mm forward PCB seating lands** and attempted to capture the OLED within the carrier alone.

The first Rev P implementation is also rejected for retention because rear
insertion passed the OLED beyond the only positive shoulder and left forward
handling retention to assumed edge friction. Its hard-stop architecture and
optical chain remain useful; its open rear window is superseded by §8.3.

The approved corrective direction is: **flush-side OLED insertion onto fixed
rear PCB datum pads; four sprung mounting-hole posts providing X/Y location and
positive loose-carrier retention; a controlled local exception for verified
snap noses only; separate carrier-to-Perspex structural hard stops; prepared
front-side protrusion no more than 1.00 mm; no separate retainer bar; and physical
retention testing before release. The successful Rev P.2 architecture is now to
be retained while the complete lighting-unit-side end rail and integral cable-tie
projection are removed, leaving the post pedestals connected locally to the side
uprights and the original Decca lighting assembly entirely unobstructed. The M2
heat-set inserts and replacement screws are also deleted: the carrier shall use
rear-accessible, anti-rotation pockets for the original 3.80 mm six-sided,
1.40 mm head-seat-depth, 10.00 mm-long matching nuts and retain the original
non-standard-thread front bolts at exactly 49.00 mm pitch. The synthetic Rev P.3
lighting keepout component is rejected and shall be removed. The carrier itself
shall close the rear of the OLED bay as an integral opaque light shield, with
only the local opening for the four input/header pins and wiring. Rev P.5 shall
reduce the carrier depth to 6.00 mm, enlarge that finished opening to
14.00 × 4.19 mm, add two envelope-contained internal side light blocks, rotate
the complete OLED reference so the connector is at the bottom, then place both
carrier fixing centres 7.00 mm farther toward that bottom relative to the OLED
group while leaving the original Perspex holes fixed at exactly 49.00 mm
horizontal pitch. The earlier active-area-bottom alignment rule is superseded;
the screen is intentionally raised 7.00 mm relative to that datum. Both
remaining plain posts are deleted and replaced by sprung locating-and-retaining
posts, subject to direct four-hole glass-clearance and complete four-post force,
strain, PCB-bow and release validation.**
