LeweeLewee/Decca/docs/Development Handover.md

# Development Handover

> **Last updated:** 2026-09-21
> **Repository:** `LeweeLewee/Decca`  
> **Authoritative branch:** `main`

This document is the durable handover for firmware development and maintenance.
Read it before relying on chat history.

## Read first

1. `CLAUDE.md`
2. `docs/Open Issues.md`
3. `docs/Specification.md`
4. `docs/Firmware Architecture.md`
5. `docs/Hardware Architecture.md`
6. `docs/Wiring.md`
7. `docs/Build Guide.md`
8. Relevant ADRs under `docs/adr/`

Always inspect the live `main` branch before changing code. Historical chat
messages and old revision-history entries may describe superseded hardware.

See [Phase 2 commissioning record](Phase%202%20Commissioning.md) for the
consolidated setup, acceptance evidence and chat-retirement record.

## Current firmware state

The production `src/main.cpp` initialises the safe board state, buttons, logical
power, display, lighting and authenticated ArduinoOTA. It continuously services
the original on/off switch, pots, VHF source, Stereo/Mono lighting request,
display and OTA without blocking. Phase 2 WiiM coordination runs on a separate
core-0 worker. Firmware v0.28.6-s1 is installed by authenticated OTA (2026-09-21).
Fresh version discovery and OTA authentication rejection passed; the owner confirmed display, standby/wake, source and volume
acceptance on 2026-09-22. See [OTA Candidate](OTA%20Candidate.md).
It retains disabled Wi-Fi sleep and requests a 20 dBm TX ceiling; device
readback is 19.5 dBm. Post-update packet loss remains OPEN as FW-WIFI-01.
The following physical acceptance was recorded on v0.28.4 (`3195c95`).
Digital and vinyl audio, channel routing, source response, network recovery,
standby display behaviour and direct-trigger acceptance pass. The owner confirmed
all formal noise/interference checks passed with no issues on 2026-09-21,
completing Phase 2 physical acceptance. The owner approved PR #11 for review and explicitly authorised merge on
2026-09-21.
Final lighting hardware acceptance remains open as HW-LGT-01.

Implemented modules:

| Module | State |
|---|---|
| `hardware` | Pin map and safe initialisation implemented |
| `settings` | NVS persistence implemented, schema version 3 |
| `buttons` | On/off, sole VHF contact and Stereo/Mono lighting request, 25 ms non-blocking debounce |
| `pots` | Four filtered/calibrated ADC1 inputs |
| `display` | Fitted-Perspex SH1106 UI physically accepted; calibrated views, top-left controller RSSI, distinct connectivity faults and idle/standby display-off protection |
| `lighting` | Safe-off PWM with immediate updates for every transition |
| `ota` | Authenticated LAN OTA as unique `decca-esp32`, reconnect handling, dual-app partitions |
| `power` | GPIO-independent logical on/standby state implemented and tested |
| `wiim` | Phase 2 local-HTTPS source, direct absolute volume over a reusable connection, source-priority/reconciliation, stop, player state, metadata and failure hysteresis implemented and live-tested |
| Main orchestration | Power, pots, VHF source, fitted display, lighting command, persistent connectivity UI, WiiM snapshots and OTA integrated; installed Phase 2 physical acceptance passed, including owner-confirmed noise sweep on 2026-09-21 |

The ESP32 is control/UI only. It never carries or processes audio.

## Accepted source logic

The original selector PCB remains as a mechanical carrier, but only the VHF
state is reliable electrically:

| VHF contact | Logical source | WiiM action |
|---|---|---|
| Closed / latched | Digital Streamer | Restore phone-controlled digital playback |
| Open / released | Vinyl | Select Line-In |

GPIO26/D26 is the physically verified sole source input. The VHF-derived pair uses two
Black conductors, with either conductor connected to GPIO26 and the other to
GND. GPIO13, GPIO16, GPIO17, GPIO19 and GPIO23 are released. GPIO25/D25 is assigned to
the separate Stereo/Mono contact. SW, MW, LW and Gram have no individual
firmware function; their interlocked release of VHF selects Vinyl. A replacement
button panel is deferred. The retained Stereo/Mono switch fault is open as HW-SW-01.

## Confirmed controller wiring

| Function | ESP32 | Physical status |
|---|---:|---|
| Volume | GPIO32/D32 | Bench-verified, 0 / about 2047 / 4095 |
| Bass | GPIO33/D33 | Bench-verified, 0 / about 2047 / 4095 |
| Treble | GPIO34/D34 | Bench-verified, 0 / about 2047 / 4095 |
| Balance | GPIO35/D35 | Bench-verified, 0 / about 2047 / 4095 |
| VHF source contact | GPIO26/D26 | Physically verified |
| OLED SDA | GPIO21/D21 | Bench-verified |
| OLED SCL | GPIO22/D22 | Bench-verified |
| On/off | GPIO14/D14 | Physically verified, closed = on / open = standby |
| Stereo/Mono lighting request | GPIO25/D25 | Firmware logic verified; retained switch fault open as HW-SW-01 |
| Dial-light PWM | GPIO18/D18 | Physically verified with installed DFR0457/three-lamp load |

Final H4 OLED loom, physically confirmed 2026-08-30:

| Wire | OLED | ESP32 |
|---|---|---|
| Brown | GND | GND |
| Red | VCC | 3V3 |
| Orange | SCL | GPIO22/D22 |
| Yellow | SDA | GPIO21/D21 |

Orange and Yellow are signal wires in H4. Neither is a 5 V conductor.

## Completed evidence

- Four pots passed on target with full 0–4095 travel and clockwise increase.
- Pi Hut 1.3-inch 128×64 white SH1106 OLED was electrically verified at address
  0x3C and physically accepted behind the final Perspex on 2026-08-30. Output is
  rotated 180 degrees; the measured viewport is X4–123/Y10–61 and normal content
  is restricted to Y24–60 for viewing-angle readability. Contrast 0x80 and the
  focused identity, control, source, metadata, play/pause and standby layouts
  were accepted from physical photographs. The calibration pattern remains a
  service diagnostic.
- VHF was accepted on GPIO26 as the only reliable active selector; every other
  interlocked position releases it and selects Vinyl.
- GPIO14/D14 was physically verified with the retained H2 Red/Green switch.
  Closed selects logical ON and open selects STANDBY; both transitions were
  accepted on the production firmware.
- Revised button logic passed strict host compilation and its nine-case harness.
- Lighting logic passed strict host compilation and its seven-case harness.
- OTA logic passed strict host compilation and its five-case harness.
- USB-to-OTA physical acceptance passed on 2026-08-30: the authenticated
  `esp32dev-ota` upload succeeded and the rebooted ESP32 reported
  `[OTA] ready at 192.168.x.x (decca.local)`.
- The accepted controls/source/display `esp32dev` release build passed and all
  eight on-target suites passed 53/53 tests on 2026-08-30 (buttons 9, display 15,
  hardware 3, lighting 7, OTA 5, pots 6, power 5 and settings 3). Production
  firmware was restored by USB; serial reported `[POWER] state=ON` and
  `[OTA] ready at 192.168.x.x (decca.local)`.
- After the previous TX2/GPIO17 Stereo/Mono integration, the release build
  passed and all eight
  on-target suites passed 55/55 (buttons 11, display 15, hardware 3, lighting 7,
  OTA 5, pots 6, power 5 and settings 3).
- After production lighting coordination and settings schema v3, the
  credential-enabled release build passed (RAM 49,936 bytes / 15.2%; flash
  839,253 bytes / 64.0%) and all eight on-target suites again passed 55/55.
- Display mount Rev P.5 is released and physically validated.
- Root documentation and the final OLED loom colours were reconciled at chat
  close-out.

Do not convert host validation into an on-target claim. Record future physical
results explicitly.

## Completed gate before mounting the ESP32

USB-to-OTA physical acceptance **passed on 2026-08-30**. The authenticated
`esp32dev-ota` upload succeeded and, after reboot, serial reported
`[OTA] ready at 192.168.x.x (decca.local)`. The procedure is retained below for
future controller replacement or recovery.

On the user's Windows machine, `pio` is not currently on PATH. Use the
PlatformIO executable directly:

```powershell
$pio = "$env:USERPROFILE\.platformio\penv\Scripts\platformio.exe"
& $pio --version
& $pio device list
```

Never type the literal placeholder `COM_PORT`. Set the actual port reported by
`device list`, for example:

```powershell
$port = "COM5"
& $pio test -e esp32dev -f test_ota
& $pio run -e esp32dev -t upload --upload-port $port
& $pio device monitor --port $port -b 115200
```

Expected serial message:

```text
[OTA] ready at 192.168.x.x (decca.local)
```

Then exit the monitor with Ctrl+C and prove wireless upload:

```powershell
$env:DECCA_OTA_PASSWORD = "THE SAME PRIVATE PASSWORD USED IN src\secrets.h"
& $pio run -e esp32dev-ota -t upload
Remove-Item Env:DECCA_OTA_PASSWORD
```

If mDNS fails, repeat the OTA command with
`--upload-port 192.168.x.x` using the address printed by the ESP32.

`src/secrets.h` is local and gitignored. Never request, display, log or commit
the user's Wi-Fi or OTA passwords.

## Recommended firmware sequence

1. **Complete (2026-08-30):** USB-to-OTA acceptance before enclosure.
2. **Complete (2026-08-30):** full PlatformIO `esp32dev` release build and all
   eight on-target suites; latest accepted run passed 55/55 tests.
3. **Complete (2026-08-30):** fitted-Perspex display calibration, visual design
   cycle and physical acceptance.
4. **Complete:** implement the logical `power` module and physically verify
   GPIO14 on/standby display coordination in production.
5. **Complete:** production coordinates pots, persistent VHF-derived source,
   logical power, fitted display and OTA in one non-blocking loop.
6. **Complete:** GPIO18/DFR0457/three-lamp operation is physically verified;
   the historical GPIO25/MOSFET test also passed:
   safe off, smooth fades through full duty, even illumination and fade fully off.
7. **Historical (2026-08-31):** normal Stereo lighting was approved at 90% /
   duty 230 with faded transitions. v0.27.4 supersedes the transition behaviour
   and applies both brightness states immediately.
8. **Historical pass (2026-08-30):** original Stereo/Mono switch wired to
   TX2/GPIO17 and GND. Physical snapshots confirmed Stereo open requests dial
   lights on and Mono closed requests them off. GPIO25 load remained disabled
   during testing. Current firmware uses GPIO25/D25; its logic is correct, but
   the retained switch fault remains open as HW-SW-01.
9. **Open — HW-LGT-01:** DFR0457 is installed on GPIO18 and the initial steady-light test
   reports no flicker. Firmware v0.27.3 at commit `0a4d3bd` is installed by
   authenticated OTA. The owner confirmed the v0.27.3 startup and D18 on path;
   the earlier v0.27.1 release retains approval for the 2.2-second version hold
   and both approximately 4.34-second 0–85% fades. Mono/off re-verification is
   blocked by HW-SW-01.
   Install the ordered WAGO star points, recheck pot/display stability with
   lamps on, then temperature and installed lamp current before closing.
10. **Deployed, physical verification pending (v0.27.4):** the fade engine is
    removed. After the 25 ms debounce, Stereo applies duty 217 immediately and
    Mono applies duty 0 immediately; power transitions are also immediate.
    Authenticated OTA succeeded and the controller returned at its reserved address.
11. **Deployed, WiiM-only acceptance passed (v0.28.0):** source commit `d06e357`
    is installed by authenticated OTA. VHF/Line-In mapping, active metadata,
    direct absolute volume/app reflection, logical-OFF stop, resume, persistent
    outage indication and automatic recovery passed. Exact 10%, 20% and 30%
    setpoints matched in WiiM Home; the owner confirmed the final response was
    much more responsive. The streamer/controller
    mDNS-label collision and the ZA3-dependent audio/trigger gates remain open.
12. **Deployed and trigger-accepted (v0.28.0, 2026-09-19):** source commit
    `36d84d1` adds a safe one-step downward volume pulse on logical power-on,
    followed by immediate restoration to the requested value. This wakes the
    WiiM and ZA3 even when a stopped TIDAL Connect session cannot be resumed by
    the local transport API. Authenticated OTA reached 100%, the controller
    returned, 30-second trigger standby passed and switch-only wake passed.
    Digital audio and left/right routing pass; vinyl and the formal noise sweep
    remain open.
13. **Deployed and responsiveness/standby accepted (v0.28.4, 2026-09-20):**
    source commit `3195c95` restores reusable secure control after a diagnostic
    regression, prioritises new physical source commands, bypasses stale retry
    cooldown and reconciles Line-In state. Vinyl passed and source response
    returned to approximately one second. The controller hostname is now
    `decca-esp32`; top-left RSSI bars and distinct controller/WiiM diagnostics are
    present. Standby shows for ten seconds, blanks and remains off during passive
    telemetry updates. The build passed at 52,336 bytes RAM / 1,018,373 bytes
    flash, both affected target suites compiled without execution, authenticated
    OTA passed, and only the formal Phase 2 noise sweep remains open.
14. **Complete (owner confirmation 2026-09-21):** all formal noise checks passed
    with no hum, buzz, clipping, switching thumps or OLED/control interference.
    FW-WIM-01 is complete; The owner approved PR #11 for review and explicitly authorised merge on 2026-09-21.
15. Keep automatic failed-boot OTA rollback as Phase 3 unless separately brought
   forward.

## Open procurement and electrical work

`docs/Open Issues.md` is the authoritative short list. Consult
`docs/Parts List.md` and the CSV BOMs for procurement detail. Immediate open
items are the ordered WAGO 221-415 distribution-connector pack and final DFR0457
immediate-transition, pot-stability, temperature, current and holder checks.
Phase 2 physical acceptance is complete, including the owner-confirmed formal
noise/interference sweep on 2026-09-21. Digital and vinyl audio, channel routing,
source response, recovery, standby behaviour and the direct WiiM-to-ZA3 trigger
are commissioned. The separate lighting and retained-switch issues remain open.

## Mechanical status

Rev Q display bezel PR [#7](https://github.com/LeweeLewee/Decca/pull/7) is
merged and owner-approved. The released Rev P.5 carrier remains frozen and
unchanged. Re-check the recorded 0.339 mm carrier clearance if either part is
reprinted on a different machine or profile.

The ESP32 controller housing **Rev C** package is now on main. The owner printed,
fitted, wired and installed it on 2026-09-07; it fitted first time. It remains a
prototype, not a production release: seven prototype and two installation gates
remain in specification v1.7.

The IEC C14 mounting plate **Rev B** is the active design. Rev A failed physical
profile review and must not be installed. Rev B uses the corrected measured
six-sided profile, passes 15/15 CAD checks and has owner confirmation of the
profile drawing; full physical fit and rear terminal/wire clearance remain open.

## Engineering guardrails

- Preserve module independence; coordinate only in `main`.
- Keep all update paths non-blocking; no `delay()` in steady-state control.
- Avoid dynamic allocation in steady state.
- Persist only through `settings`.
- Keep analogue inputs on ADC1 because Wi-Fi is active.
- Treat proposed pins as unverified until a physical test is recorded.
- Update wiring, BOM, architecture and revision history with relevant changes.
- Use Conventional Commits and do not overwrite unrelated work.
- Do not alter the frozen Rev P.5 carrier to resolve a future bezel reprint.

## New-chat handover prompt

```text
Continue development and maintenance of the Decca ESP32 restoration firmware in
https://github.com/LeweeLewee/Decca.

Before acting, read docs/Development Handover.md and docs/Open Issues.md in
full, then CLAUDE.md, docs/Specification.md, docs/Firmware Architecture.md, docs/Hardware
Architecture.md, docs/Wiring.md, docs/Build Guide.md and the relevant ADRs.
Treat the live main branch and those documents as authoritative over chat memory.

Immediate priorities: physically verify the immediate v0.28.4 lighting behavior,
repair the retained Stereo/Mono switch under HW-SW-01 and resolve HW-LGT-01.
DFR0457 is installed on GPIO18, and firmware v0.28.4 from source commit `3195c95`
is running after authenticated OTA and network-return verification. Complete the remaining WAGO installation, pot-stability,
temperature and current checks at 1 kHz and 85% / duty 217. When delivered, use
WAGO 221-415 five-way connectors as separate +5 V and common-GND star points.
The shared 5 V PSU is connected to ESP32 VIN/5V and USB is removed.

The Phase 2 branch contains the installed 85% duty 217 setting. The ESP32's
installed image is firmware v0.28.4 from source commit `3195c95`; authenticated
OTA and network return passed. Firmware releases use the single version value
in `src/version.h`; v0.28.4 holds that identifier for 2.2 seconds on the
cold-start/OTA-reboot screen and retains immediate lighting transitions.
It coordinates the acquired WiiM Pro in a background worker with a 16 KiB stack,
three-failure outage hysteresis and direct absolute-volume commands over a
worker-lifetime reusable HTTPS connection. Physical source changes take priority
over wake work, bypass stale retry cooldown and reconcile WiiM Line-In state;
installed switching is approximately one second.
Logical power-on also sends a safe one-step downward volume pulse and restores
the requested value, producing WiiM/ZA3 trigger activity without starting a
stopped network stream or exceeding the selected listening level.
Production coordination covers all four pots,
VHF-derived source, logical power and display while
continuously servicing OTA. The OLED dims after 60 s, turns pixels off after
5 min, and blanks standby after 10 s. Power transitions and on-state activity
wake it; passive telemetry while already in standby does not. The top-left
header reports controller RSSI and connectivity errors distinguish controller
Wi-Fi loss from an unresponsive WiiM. The
accepted control overlays use Volume 0–100%, Bass/Treble −50..0..+50 and Balance
L50..0..R50 with centred bars and monochrome icons.

GPIO18 PWM, VHF GPIO26/D26 and on/off GPIO14/D14 are physically verified.
Stereo/Mono uses GPIO25/D25; its switch fault is open under HW-SW-01. Final MOSFET/three-lamp
acceptance is open under HW-LGT-01. Preserve the required behaviour: Stereo and
logical power-on switch immediately to 85%; Mono and logical standby switch
immediately off. Preserve the accepted
VHF-only source logic: VHF closed = Digital
Streamer; VHF open = Vinyl/Line-In;
GPIO13, GPIO16, GPIO17, GPIO19 and GPIO23 remain unused. Preserve the final OLED loom: Brown GND,
Red 3V3 VCC, Orange SCL GPIO22, Yellow SDA GPIO21.

Keep the ESP32 control/UI-only, preserve module independence, update all affected
docs/BOM/status references with each change, verify before committing, and push
logical changes to main. Rev Q bezel PR #7 is merged, complete and approved;
the Rev P.5 carrier remains frozen.
```

## Security acceptance gate (2026-09-21)

FW-SEC-01 is open. See [Security Acceptance](Security%20Acceptance.md) before
claiming security readiness. The initial live OTA negative test passed; the
v0.28.6-s1 adds response/transport limits and security tests and is deployed;
physical acceptance passed by owner confirmation on 2026-09-22; the wider security gate remains open. See [OTA Candidate](OTA%20Candidate.md) before any upload.
