LeweeLewee/Decca/mechanical/Drawings/Decca_ESP32_Controller_Housing_revC_01_closed.png

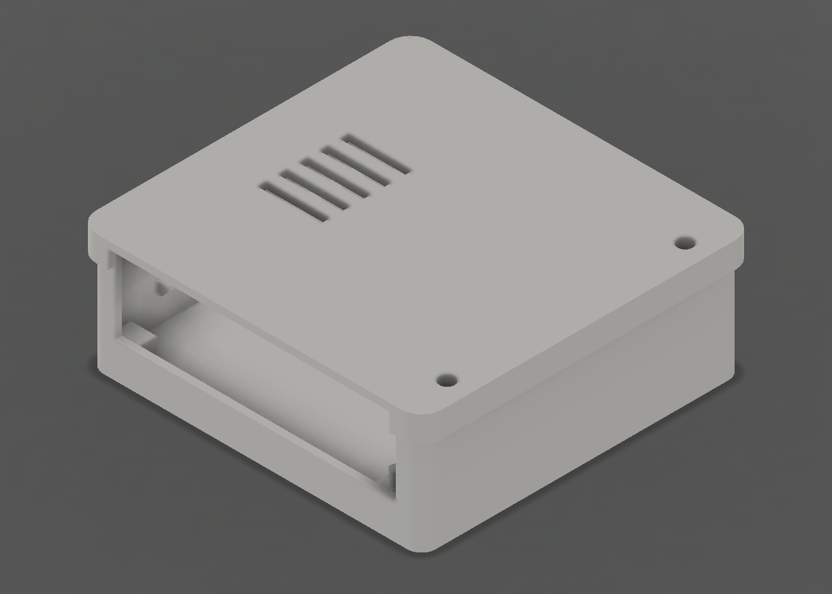
mechanical/Drawings/Decca_ESP32_Controller_Housing_revC_01_closed.png
