LeweeLewee/Decca/mechanical/Drawings/Decca_ESP32_Controller_Housing_revC_02_lid_removed.png

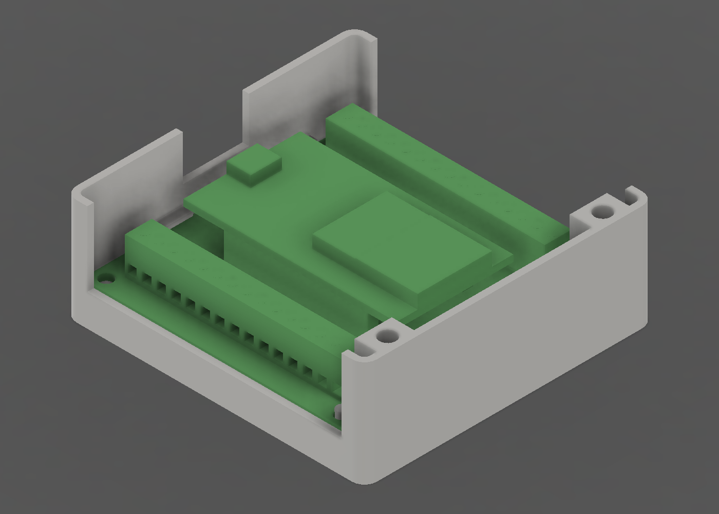
mechanical/Drawings/Decca_ESP32_Controller_Housing_revC_02_lid_removed.png
