LeweeLewee/Decca/mechanical/Drawings/Decca_ESP32_Controller_Housing_revC_03_exploded.png

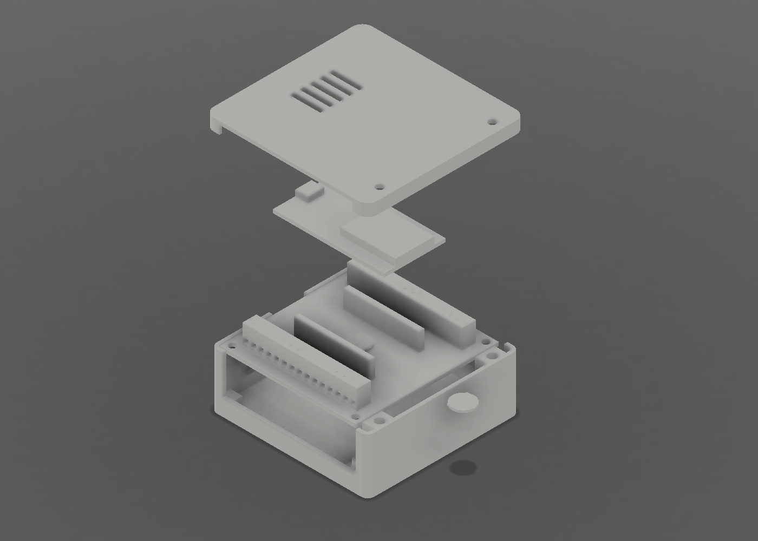
mechanical/Drawings/Decca_ESP32_Controller_Housing_revC_03_exploded.png
