LeweeLewee/Decca/mechanical/Drawings/Decca_ESP32_Controller_Housing_revC_04_plan.png

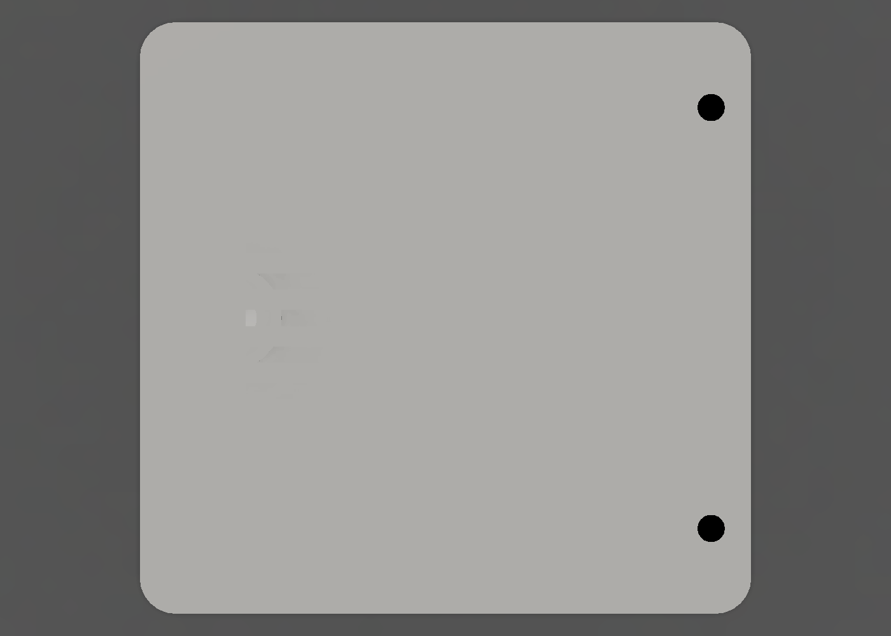
mechanical/Drawings/Decca_ESP32_Controller_Housing_revC_04_plan.png
