LeweeLewee/Decca/mechanical/Drawings/Decca_ESP32_Controller_Housing_revC_05_elevation.png

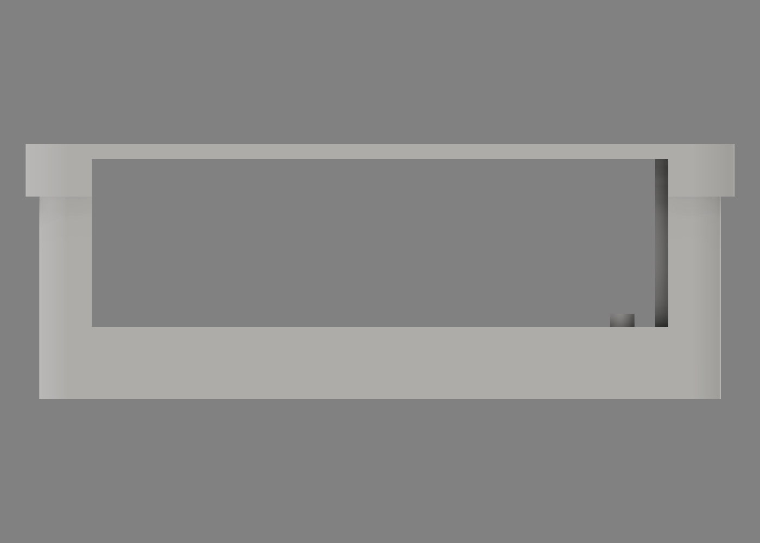
mechanical/Drawings/Decca_ESP32_Controller_Housing_revC_05_elevation.png
