LeweeLewee/Decca/mechanical/Drawings/Decca_ESP32_Controller_Housing_revC_06b_terminal_entry_iso.png

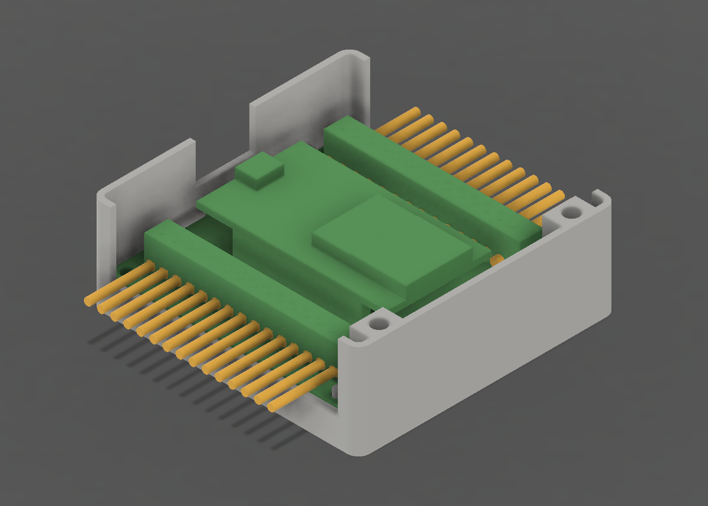
mechanical/Drawings/Decca_ESP32_Controller_Housing_revC_06b_terminal_entry_iso.png
