LeweeLewee/Decca/mechanical/Drawings/Decca_ESP32_Controller_Housing_revC_06c_terminal_entry_section.png

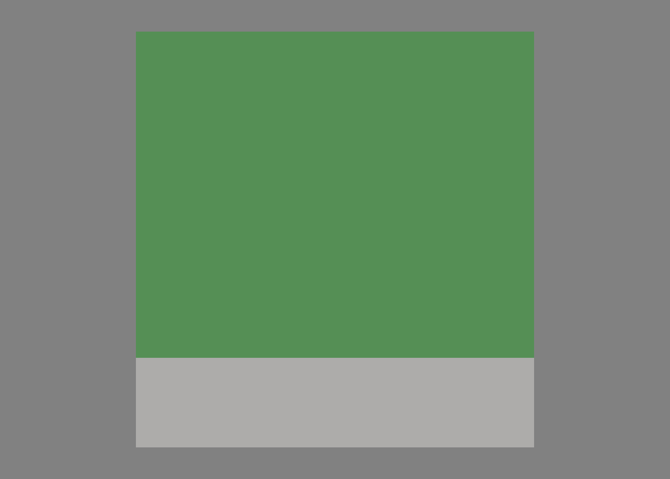
mechanical/Drawings/Decca_ESP32_Controller_Housing_revC_06c_terminal_entry_section.png
