LeweeLewee/Decca/mechanical/Drawings/Decca_ESP32_Controller_Housing_revC_07_entry_corridors.png

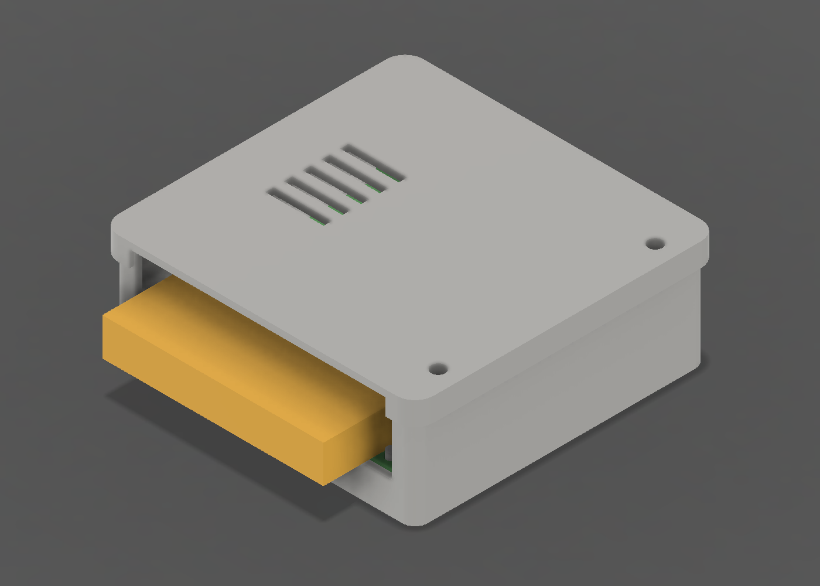
mechanical/Drawings/Decca_ESP32_Controller_Housing_revC_07_entry_corridors.png
