LeweeLewee/Decca/mechanical/Drawings/Decca_ESP32_Controller_Housing_revC_09_cover_removal_wired.png

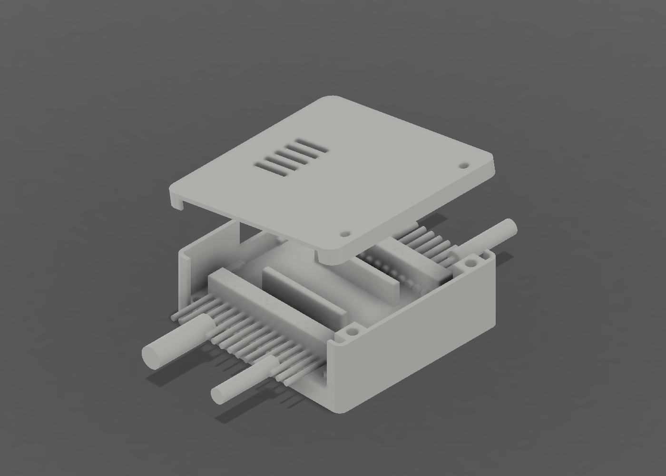
mechanical/Drawings/Decca_ESP32_Controller_Housing_revC_09_cover_removal_wired.png
