LeweeLewee/Decca/mechanical/Drawings/Decca_ESP32_Controller_Housing_revC_09b_cover_removal_end.png

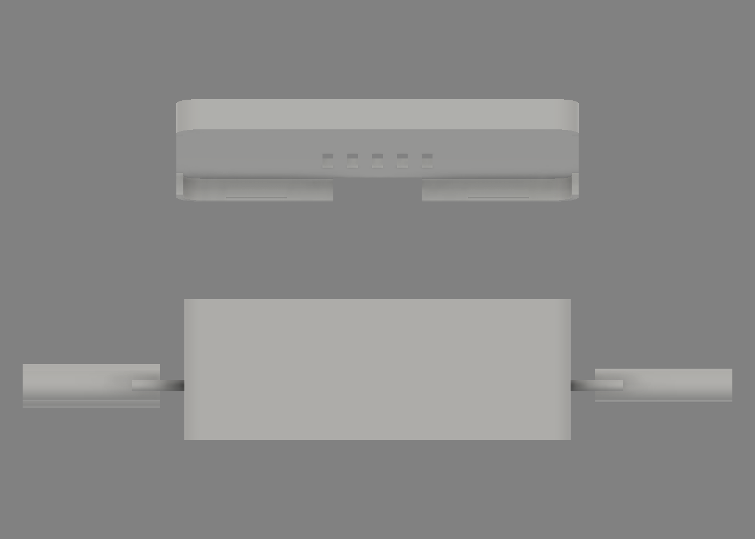
mechanical/Drawings/Decca_ESP32_Controller_Housing_revC_09b_cover_removal_end.png
