LeweeLewee/Decca/mechanical/Drawings/Decca_ESP32_Controller_Housing_revC_12_cabinet_fixings.png

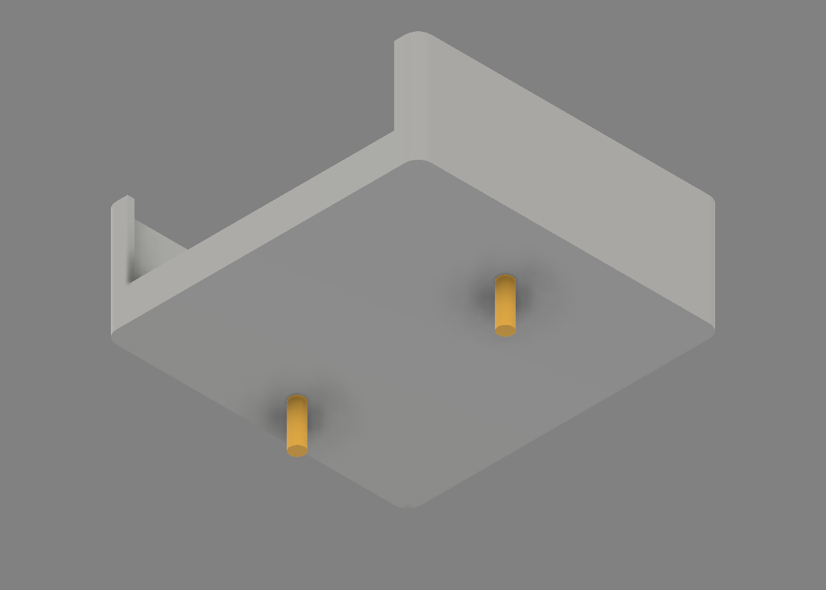
mechanical/Drawings/Decca_ESP32_Controller_Housing_revC_12_cabinet_fixings.png
