LeweeLewee/Decca/mechanical/Drawings/Decca_ESP32_Controller_Housing_revC_14_retention.png

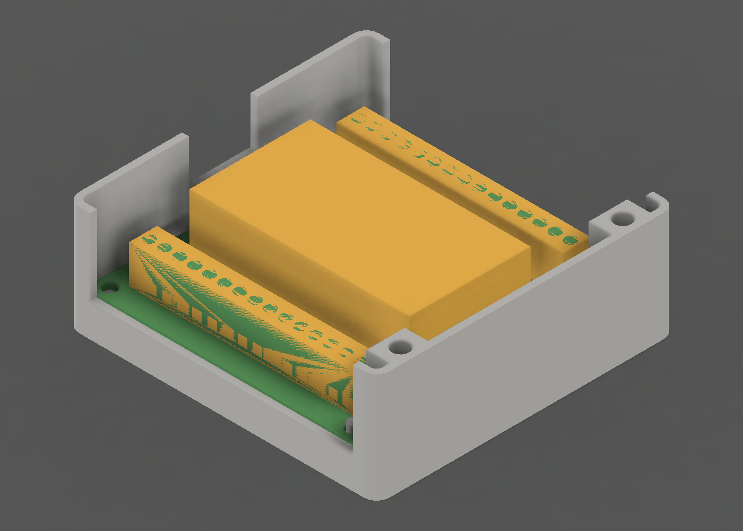
mechanical/Drawings/Decca_ESP32_Controller_Housing_revC_14_retention.png
