LeweeLewee/Decca/mechanical/Drawings/Decca_ESP32_Controller_Housing_revC_14b_locating_posts.png

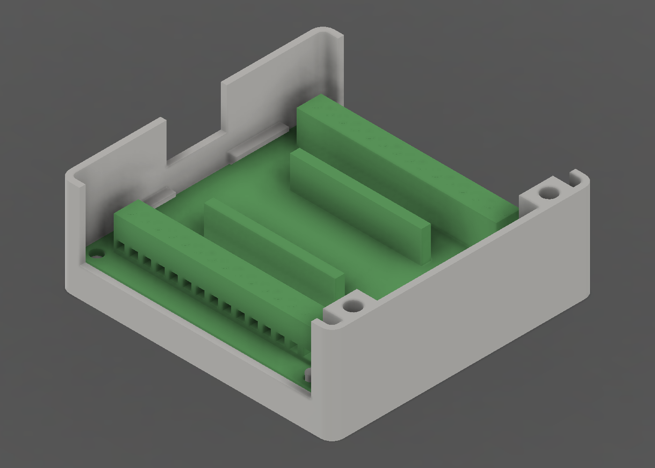
mechanical/Drawings/Decca_ESP32_Controller_Housing_revC_14b_locating_posts.png
