LeweeLewee/Decca/mechanical/Drawings/Decca_ESP32_Controller_Housing_revC_15_section.png

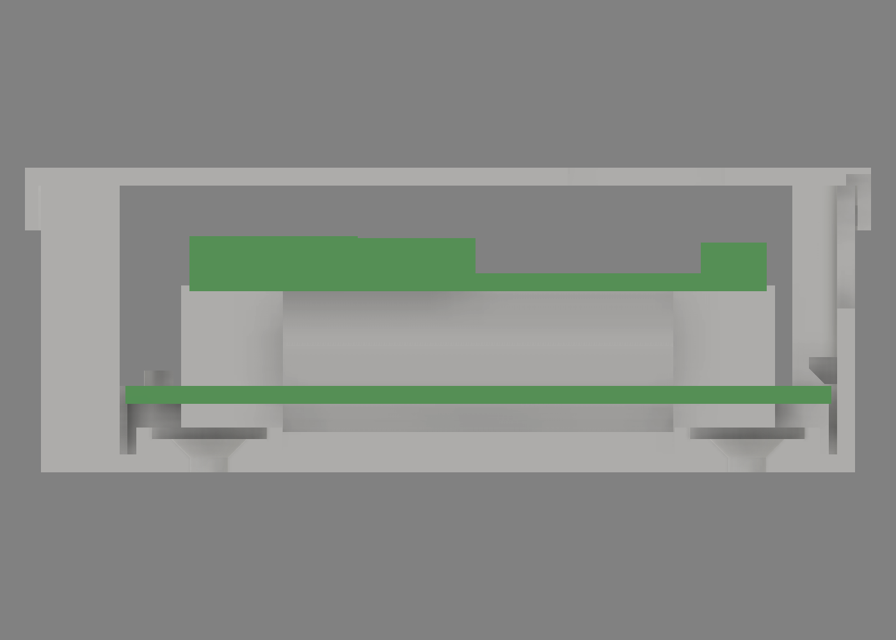
mechanical/Drawings/Decca_ESP32_Controller_Housing_revC_15_section.png
