LeweeLewee/Decca/mechanical/Drawings/Decca_IEC_C14_Mounting_Plate_revA_views.png

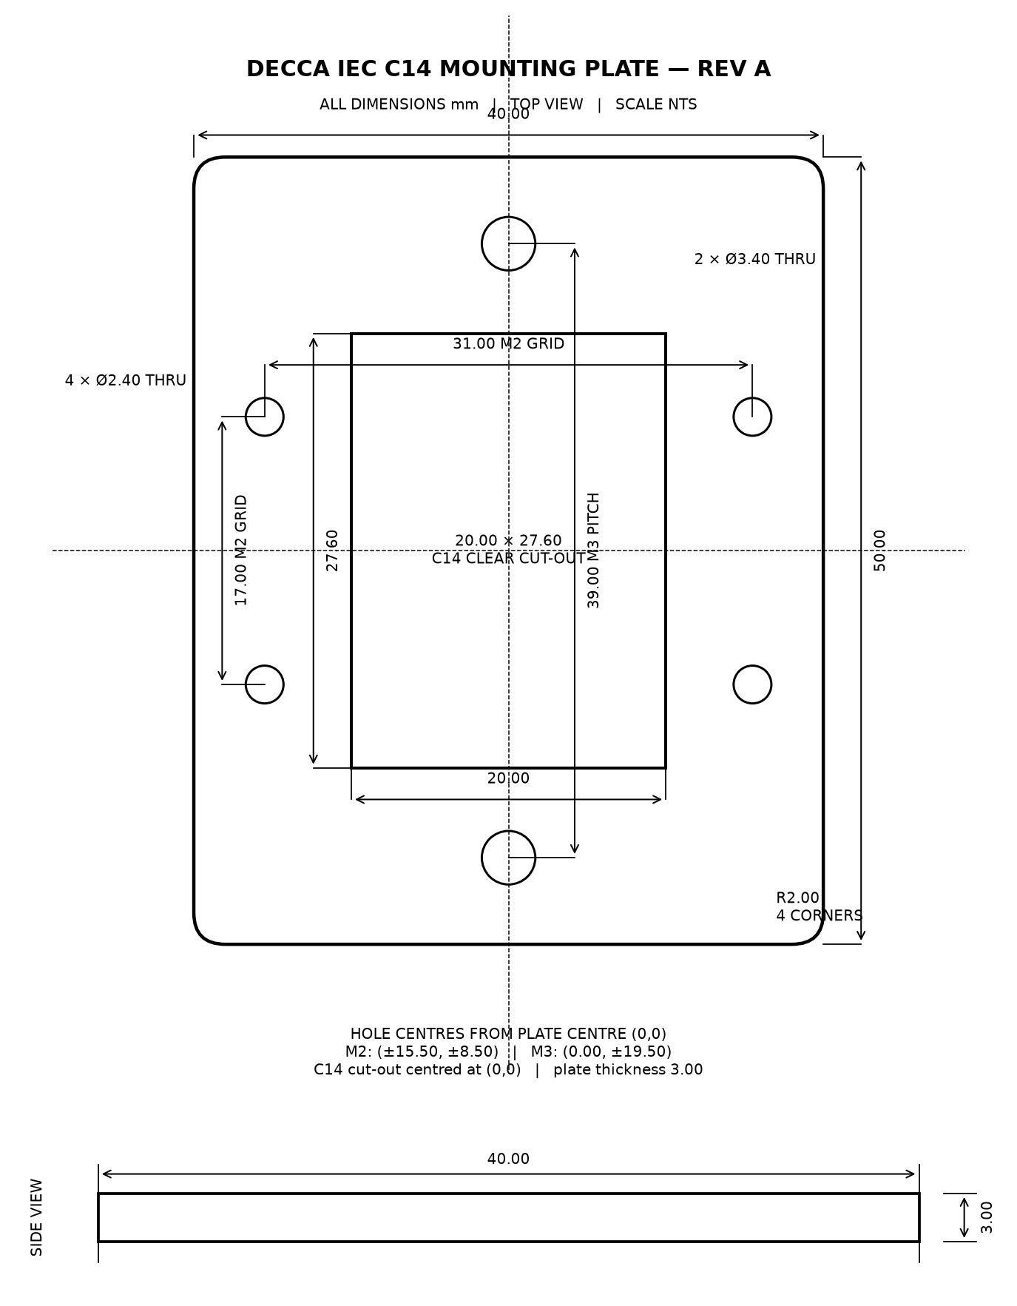
mechanical/Drawings/Decca_IEC_C14_Mounting_Plate_revA_views.png
