LeweeLewee/Decca/mechanical/Drawings/Decca_IEC_C14_Mounting_Plate_revB_views.png

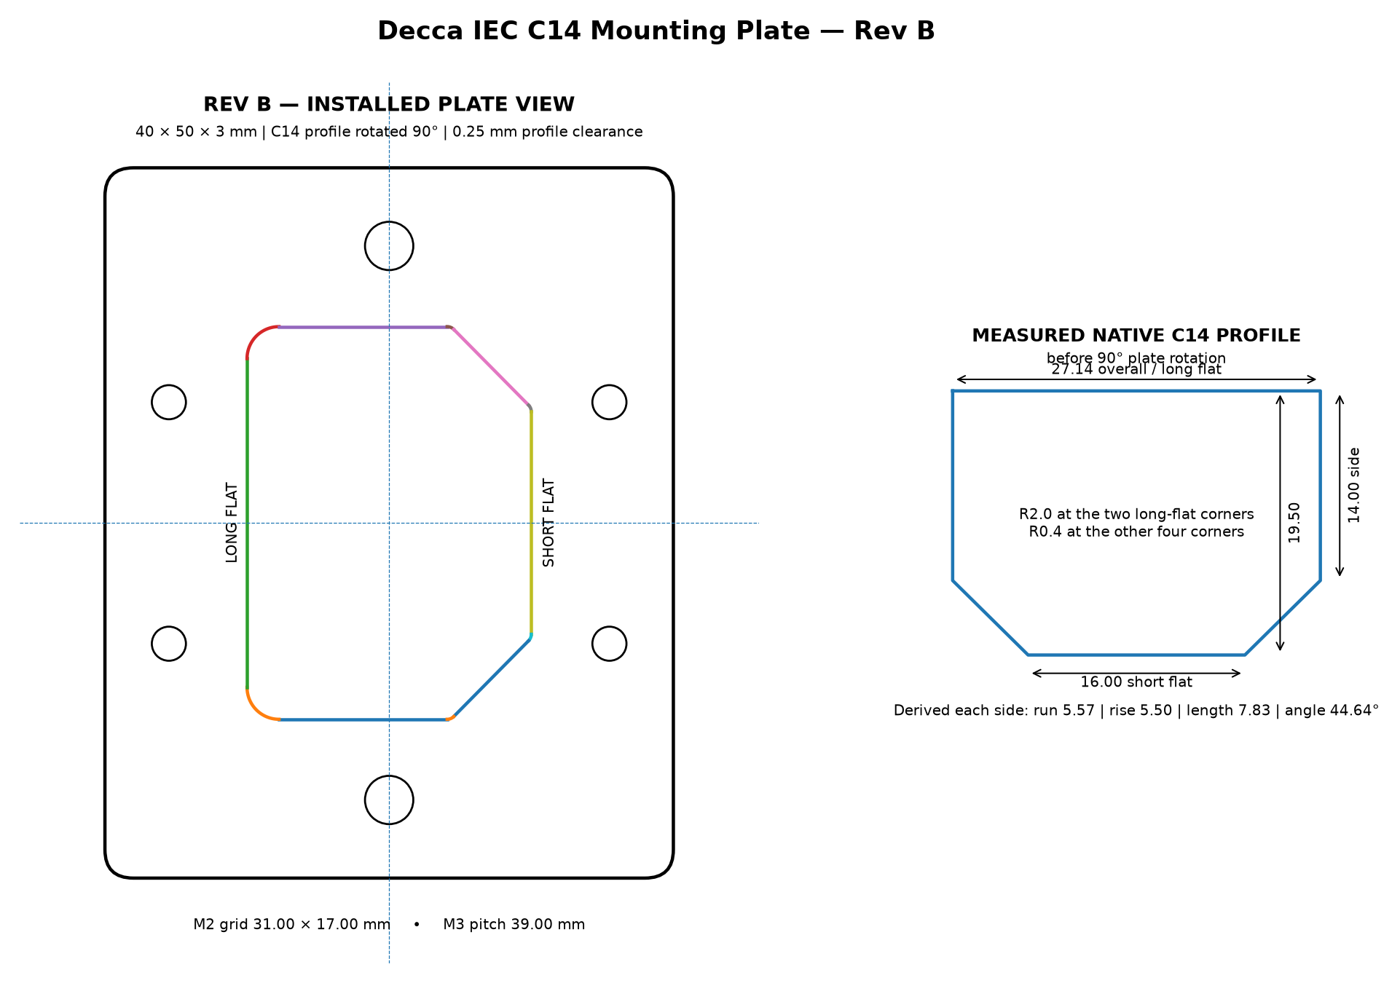
mechanical/Drawings/Decca_IEC_C14_Mounting_Plate_revB_views.png
