LeweeLewee/Decca/mechanical/Drawings/Decca_OLED_Display_Bezel_revQ_lip_oblique.png

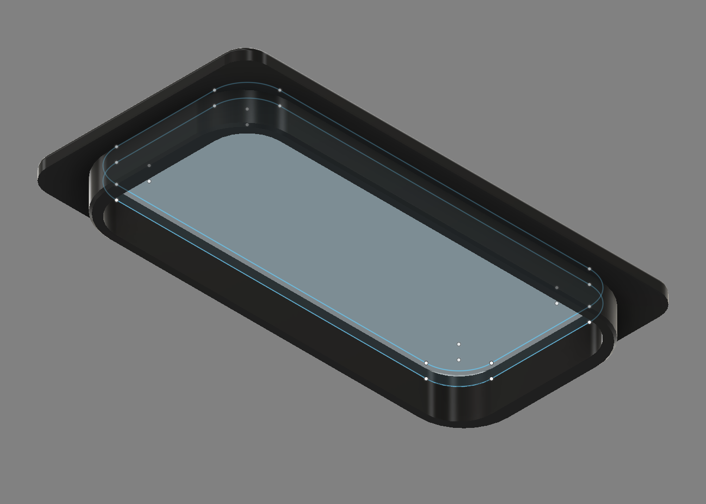
mechanical/Drawings/Decca_OLED_Display_Bezel_revQ_lip_oblique.png
