LeweeLewee/Decca/mechanical/Drawings/Decca_OLED_Display_Bezel_revQ_oblique.png

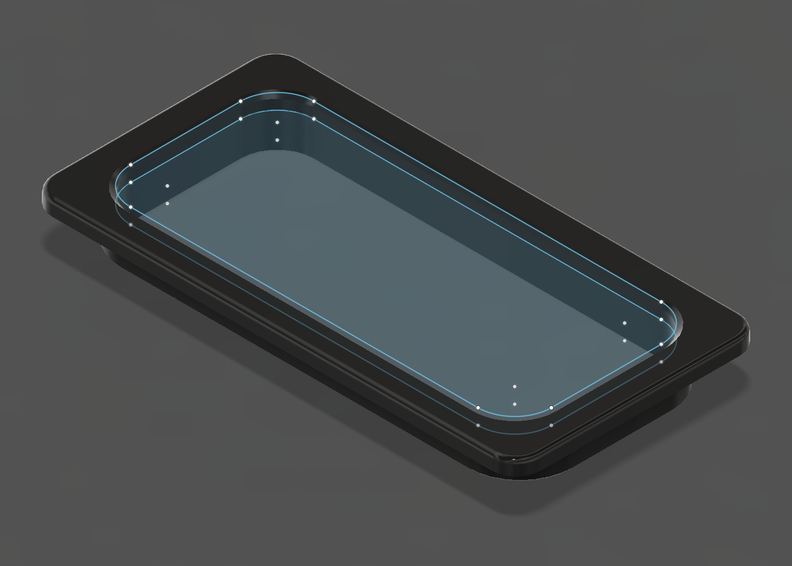
mechanical/Drawings/Decca_OLED_Display_Bezel_revQ_oblique.png
