LeweeLewee/Decca/mechanical/Drawings/Decca_OLED_Display_Bezel_revQ_rear.png

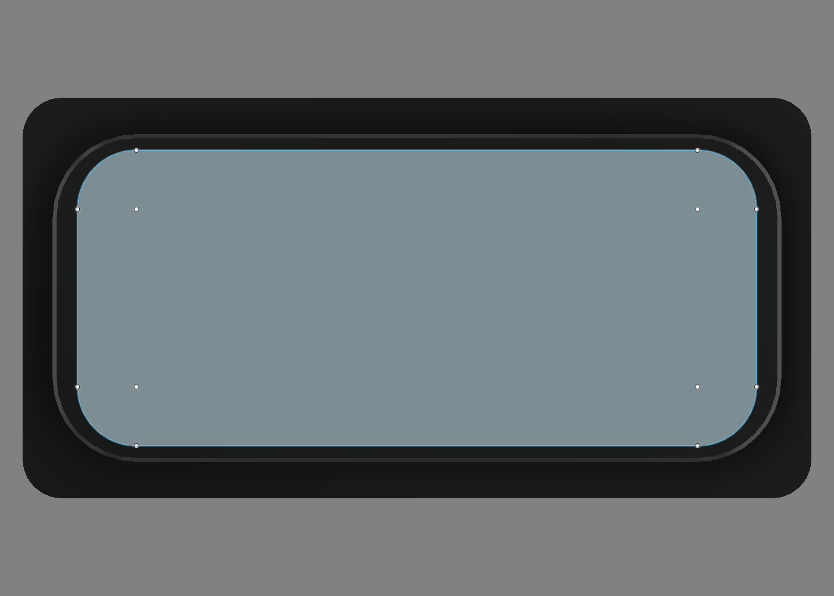
mechanical/Drawings/Decca_OLED_Display_Bezel_revQ_rear.png
