LeweeLewee/Decca/mechanical/Drawings/Decca_OLED_Display_Bezel_revQ_section.png

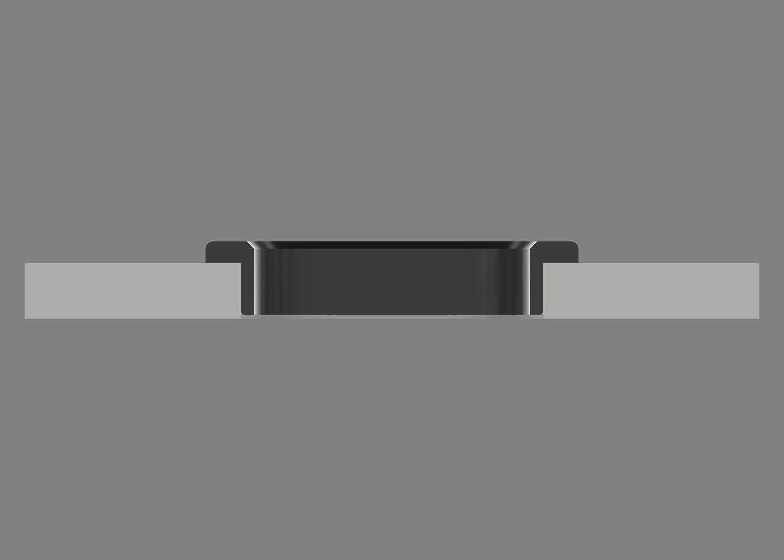
mechanical/Drawings/Decca_OLED_Display_Bezel_revQ_section.png
