LeweeLewee/Decca/mechanical/CAD/Rear_Display_Carrier_revP.step

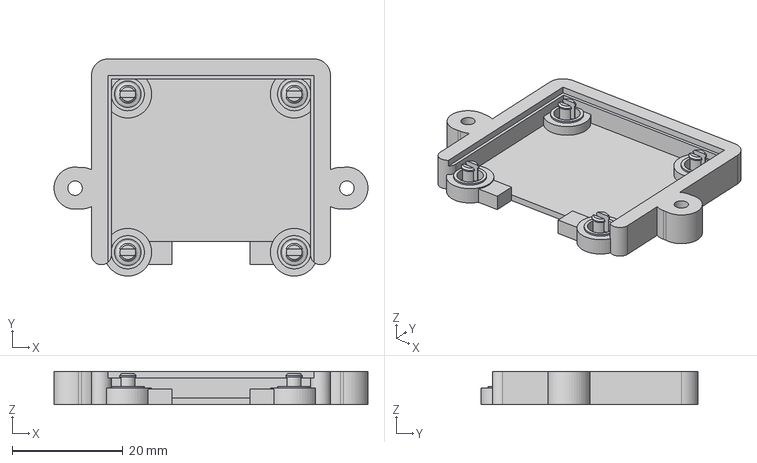
[picture p42: CAD file, 2026-08-30]
mechanical/CAD/Rear_Display_Carrier_revP.step
56.6 x 39.1 x 6.00 mm
