LeweeLewee/Decca/mechanical/CAD/Hex_Pocket_Fit_Coupon_revP.step

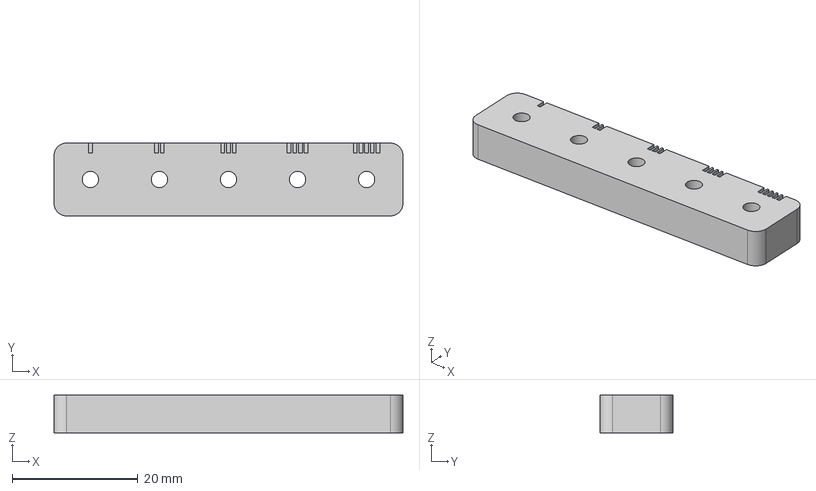
[picture p43: CAD file, 2026-08-30]
mechanical/CAD/Hex_Pocket_Fit_Coupon_revP.step
55.6 x 11.6 x 6.00 mm
