LeweeLewee/Decca/mechanical/CAD/Rear_Display_Carrier_revN.step

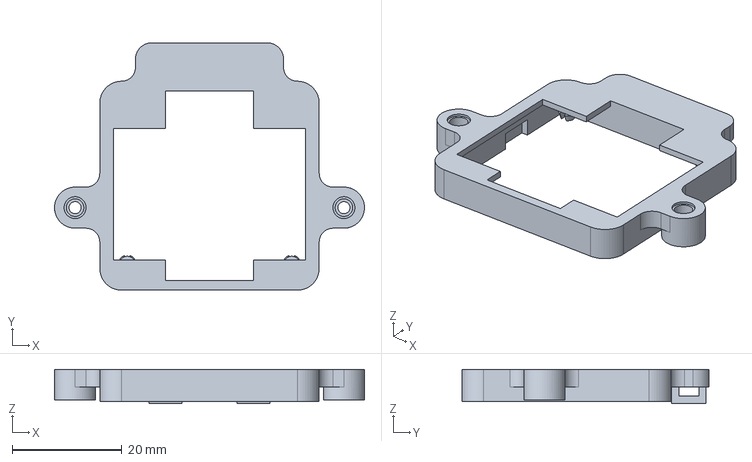
[picture p44: CAD file, 2026-08-28]
mechanical/CAD/Rear_Display_Carrier_revN.step
56.5 x 45.1 x 6.20 mm
