LeweeLewee/Decca/mechanical/CAD/Retainer_Bar_revN.step

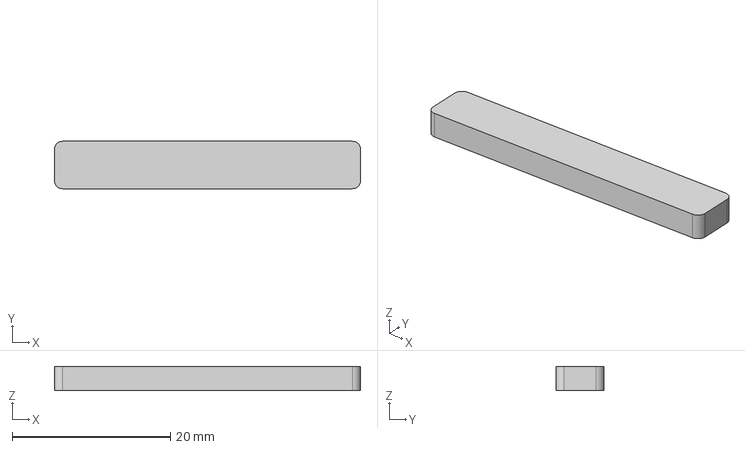
[picture p45: CAD file, 2026-08-28]
mechanical/CAD/Retainer_Bar_revN.step
38.6 x 6.00 x 3.05 mm
