LeweeLewee/Decca/mechanical/CAD/Retainer_Bar_revM.step

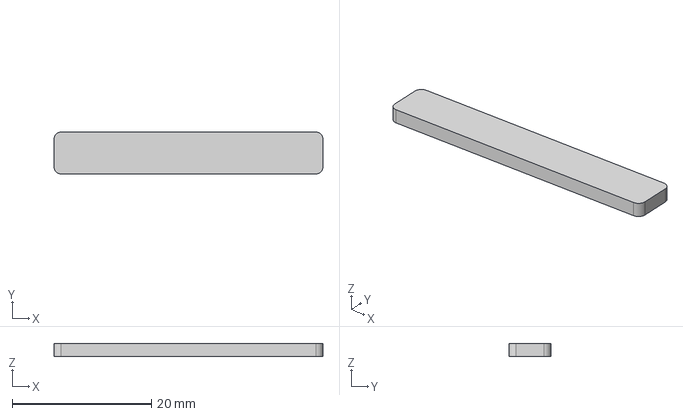
[picture p46: CAD file, 2026-08-28]
mechanical/CAD/Retainer_Bar_revM.step
38.6 x 6.00 x 1.85 mm
