LeweeLewee/Decca/mechanical/CAD/Front_Bezel_revN.step

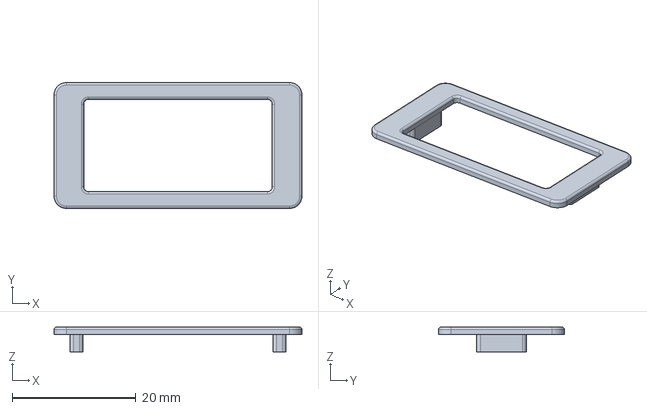
[picture p47: CAD file, 2026-08-27]
mechanical/CAD/Front_Bezel_revN.step
40.0 x 20.3 x 4.00 mm
