LeweeLewee/Decca/mechanical/CAD/Front_Bezel_revE.step

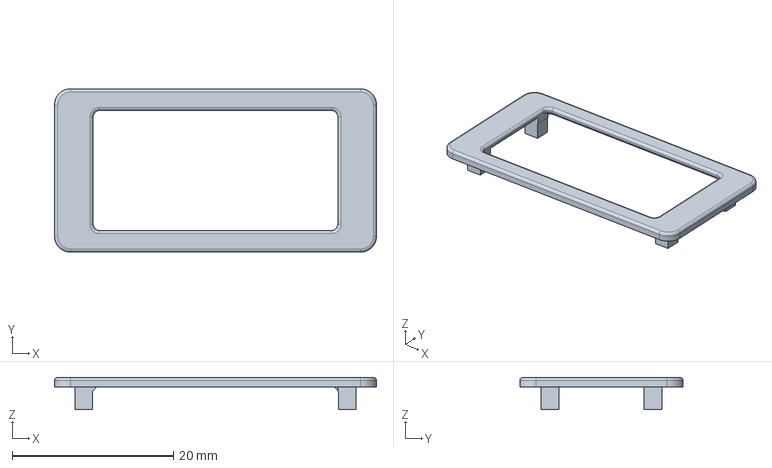
[picture p48: CAD file, 2026-08-27]
mechanical/CAD/Front_Bezel_revE.step
40.0 x 20.3 x 4.00 mm
