LeweeLewee/Decca/src/display.h

/**
 * @file    display.h
 * @brief   SH1106 OLED display mounted behind the dial glass.
 *
 * display owns the 1.3-inch 128x64 I2C panel and everything drawn to it. It
 * renders state supplied by main and never reads input modules directly.
 *
 * Responsibility: render local state, animated startup, transient controls,
 *                 and Phase 2-ready mapped-function/metadata views; own
 *                 refresh timing and the OLED driver.
 * Depends on:      hardware (I2C), settings (source type/shared state).
 * Used by:         main; does not call input or lighting modules.
 */

#pragma once

#include <cstddef>
#include <cstdint>

#include "settings.h"

namespace decca::display {

constexpr uint8_t kI2cAddress = 0x3C;
constexpr uint8_t kWidth = 128;
constexpr uint8_t kHeight = 64;
constexpr uint8_t kPanelRotation = 2;
constexpr uint8_t kViewportX = 4;
constexpr uint8_t kViewportY = 10;
constexpr uint8_t kViewportWidth = 120;
constexpr uint8_t kViewportHeight = 52;
constexpr uint8_t kContentTop = 24;
constexpr uint8_t kContentBottom = 60;
constexpr uint8_t kWifiIndicatorX = 7;
constexpr uint8_t kWifiIndicatorBaselineY = 33;
constexpr uint8_t kPanelContrast = 0x80;
constexpr uint8_t kDimmedContrast = 0x20;
constexpr uint32_t kDimAfterMs = 60'000;
constexpr uint32_t kSleepAfterMs = 300'000;
constexpr uint32_t kStandbySleepAfterMs = 10'000;
constexpr uint16_t kControlMax = 1000;
constexpr uint32_t kStartupAnimationDurationMs = 1000;
constexpr uint32_t kStartupDurationMs = 3000;
constexpr uint8_t kStartupFrameCount = 5;
constexpr uint32_t kStartupFrameIntervalMs =
    kStartupAnimationDurationMs / kStartupFrameCount;
constexpr uint32_t kStartupFinalFrameHoldMs =
    kStartupDurationMs -
    ((kStartupFrameCount - 1U) * kStartupFrameIntervalMs);
constexpr uint32_t kControlDurationMs = 2000;
constexpr uint32_t kStatusDurationMs = 1500;
constexpr uint32_t kDiagnosticDurationMs = 3000;
constexpr uint8_t kMessageCapacity = 32;
constexpr uint8_t kFunctionCapacity = 20;
constexpr uint8_t kTitleCapacity = 32;
constexpr uint8_t kArtistCapacity = 24;

/** @brief Power state shown on the Phase 1 display. */
enum class PowerState : uint8_t {
    Standby,
    On,
};

/** @brief Front-panel control represented by a transient level view. */
enum class Control : uint8_t {
    Volume,
    Bass,
    Treble,
    Balance,
};

/**
 * @brief Coherent display snapshot supplied by the top-level coordinator.
 *
 * Control values use the pots module's normalised 0-1000 scale. Text pointers
 * may be null and are copied synchronously by setState() into fixed storage;
 * callers retain no lifetime obligation. Values above the control range and
 * text beyond the documented capacities are clamped/truncated.
 */
struct ViewState {
    PowerState power = PowerState::Standby;
    settings::Source source = settings::Source::DigitalStreamer;
    uint16_t volume = 0;
    uint16_t bass = 0;
    uint16_t treble = 0;
    uint16_t balance = 0;
    const char* functionName = nullptr;
    const char* title = nullptr;
    const char* artist = nullptr;
    bool playing = false;
    /** Controller Wi-Fi strength: 0 disconnected, 1 weak, 2 fair, 3 strong. */
    uint8_t controllerWifiBars = 0;
};

/** @brief Semantic frame types used by the renderer and its test observer. */
enum class FrameKind : uint8_t {
    Startup,
    Dashboard,
    Control,
    Function,
    Status,
    Diagnostic,
    Calibration,
};

/** @brief Current OLED protection state. */
enum class PanelPowerState : uint8_t {
    Awake,
    Dimmed,
    Sleeping,
};

/**
 * @brief Initialise the purchased SH1106 panel and render the startup frame.
 * @pre   hardware::init() has run and configured I2C on GPIO21/GPIO22.
 */
void init();

/**
 * @brief Redraw only when state changes or a transient expires. Non-blocking;
 *        call once per main loop.
 */
void update();

/** @brief Return whether the SH1106 acknowledged and initialised. */
bool ready();

/** @brief Return the current contrast/display-off protection state. */
PanelPowerState panelPowerState();

/** @brief Wake the OLED and restart its inactivity timers. */
void noteActivity();

/**
 * @brief Supply a complete display snapshot; pointed-to text is copied.
 *
 * Entering standby and every on-state change wake the panel. Passive state
 * changes while already in standby are retained without waking a sleeping OLED.
 */
void setState(const ViewState& state);

/**
 * @brief Show a control name, level bar and percentage for 2 s.
 * @param control Control whose position changed.
 * @param value Normalised position; values above 1000 are clamped.
 */
void showControl(Control control, uint16_t value);

/** @brief Confirm the current mapped function for 1.5 s. */
void showFunction();

/** @brief Show a short transient status message. */
void showStatus(const char* message);

/** @brief Show a longer transient diagnostic message. */
void showDiagnostic(const char* message);

/** @brief Present the retained SW position as unavailable in Phase 1. */
void showSwUnavailable();

/**
 * @brief Hold a full-panel orientation and visible-area calibration pattern.
 *
 * The pattern remains active until hideCalibrationPattern() is called. It uses
 * the complete logical 128x64 canvas so a straight-on photograph through the
 * fitted Perspex can identify the visible pixel boundaries.
 */
void showCalibrationPattern();

/** @brief Leave calibration mode and return to the current dashboard. */
void hideCalibrationPattern();

#ifdef PIO_UNIT_TESTING
namespace testing {

struct Frame {
    FrameKind kind;
    ViewState state;
    Control control;
    uint16_t controlValue;
    uint8_t startupFrame;
    const char* firmwareVersion;
    const char* message;
};

using TimeProvider = uint32_t (*)();
using PanelBegin = bool (*)();
using FrameWriter = void (*)(const Frame& frame);

/** Format the visible value used by a control transient. */
void formatControlValue(Control control,
                        uint16_t value,
                        char* output,
                        size_t capacity);

/** Replace millis() with a deterministic provider. */
void setTimeProvider(TimeProvider provider);

/** Replace the physical SH1106 begin operation. */
void setPanelBegin(PanelBegin begin);

/** Observe semantic frames without writing to the physical OLED. */
void setFrameWriter(FrameWriter writer);

/** Restore real time and physical SH1106 operations. */
void resetHooks();

}  // namespace testing
#endif

}  // namespace decca::display
