LeweeLewee/Decca/src/secrets.example.h

/** Copy to src/secrets.h, replace placeholders, and never commit it. */
#pragma once
#define DECCA_WIFI_SSID "YOUR_WIFI_NAME"
#define DECCA_WIFI_PASSWORD "YOUR_WIFI_PASSWORD"
#define DECCA_OTA_PASSWORD "CHOOSE_A_LONG_UNIQUE_OTA_PASSWORD"
#define DECCA_WIIM_HOST "YOUR_RESERVED_WIIM_IP"
